sarvan13/Team9-Robot/ENPH257/DampedSquare.png

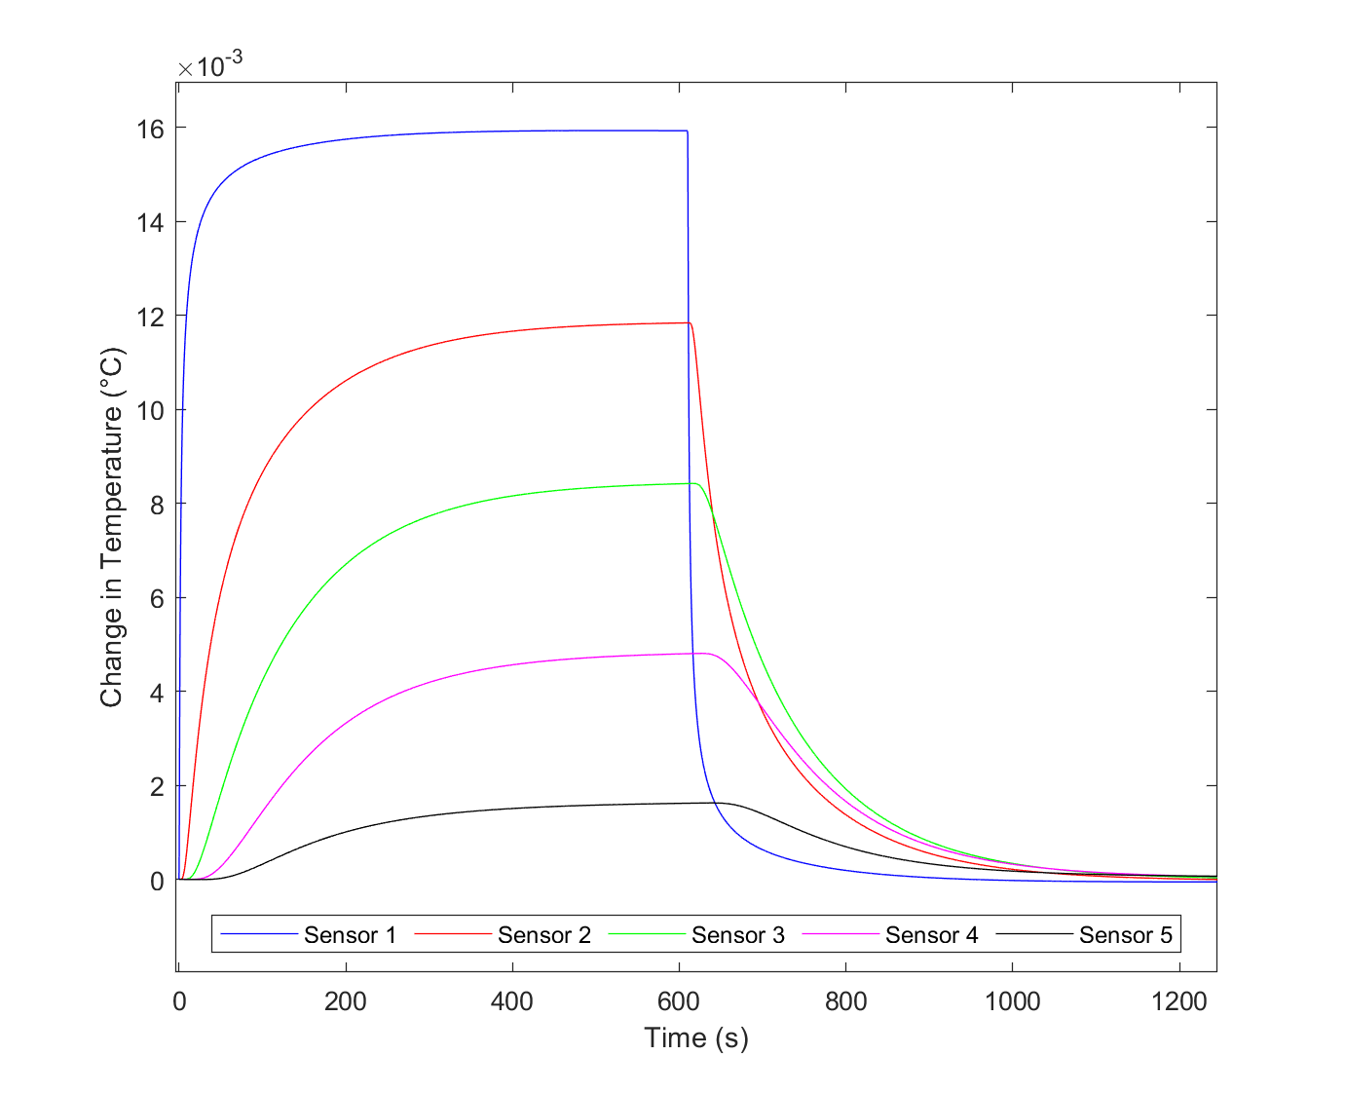
ENPH257/DampedSquare.png
