sarvan13/Team9-Robot/ENPH257/HorizontalFinal.png

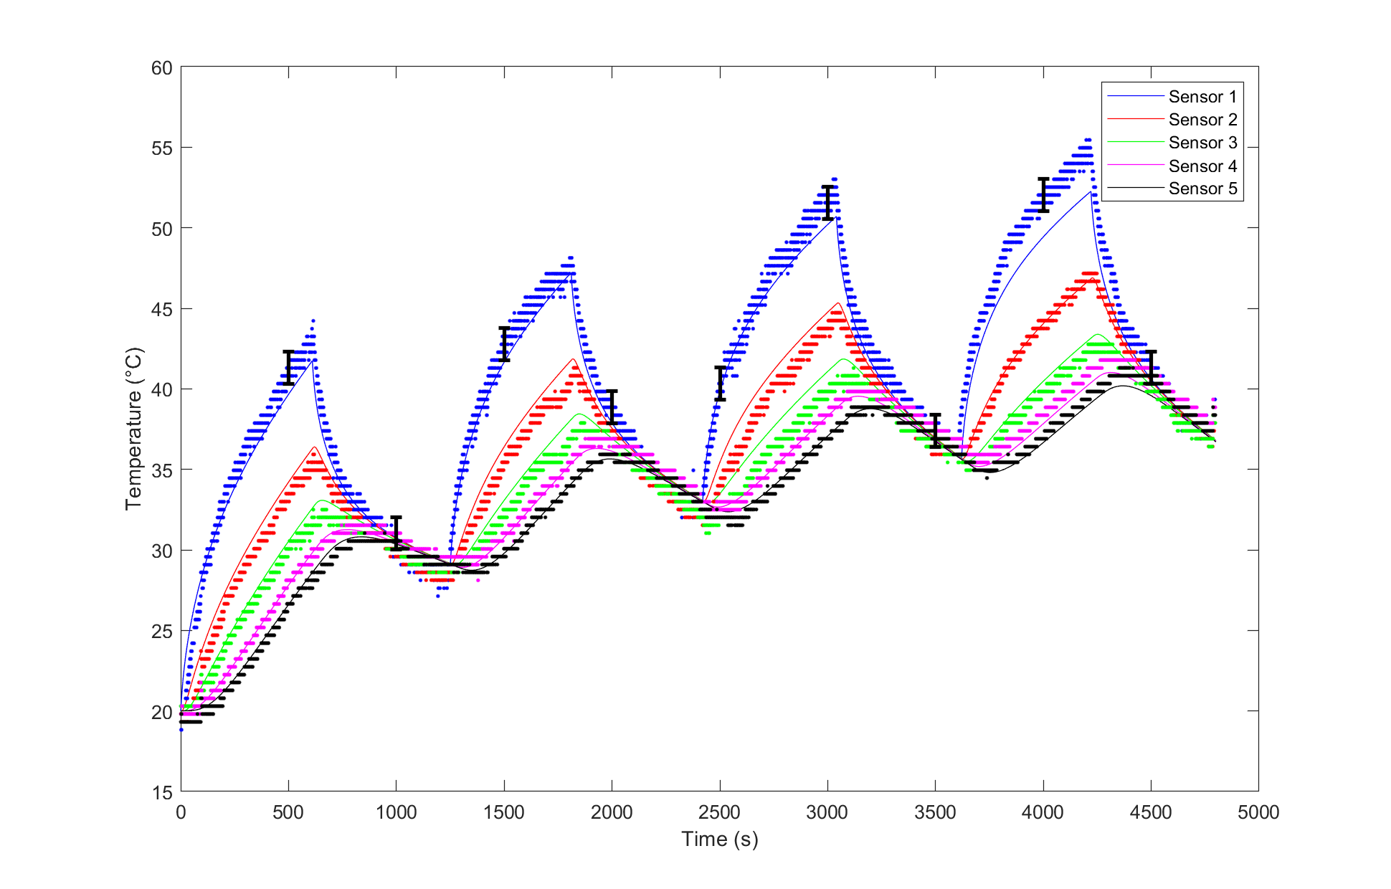
ENPH257/HorizontalFinal.png
