sarvan13/Team9-Robot/Solidworks/cutouts/chassis_cutout.SLDPRT

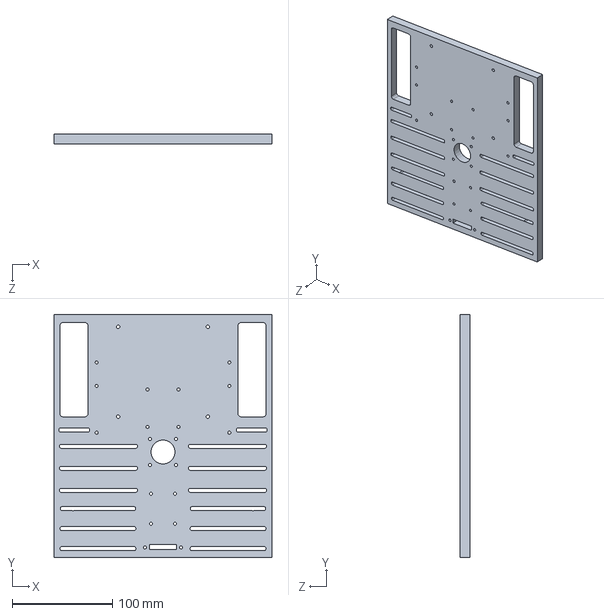
[picture p22: CAD file, 2019-07-09]
Solidworks/cutouts/chassis_cutout.SLDPRT
217.4 x 242.8 x 10.0 mm
