sarvan13/Team9-Robot/Solidworks/gears/36 teeth gear.SLDPRT

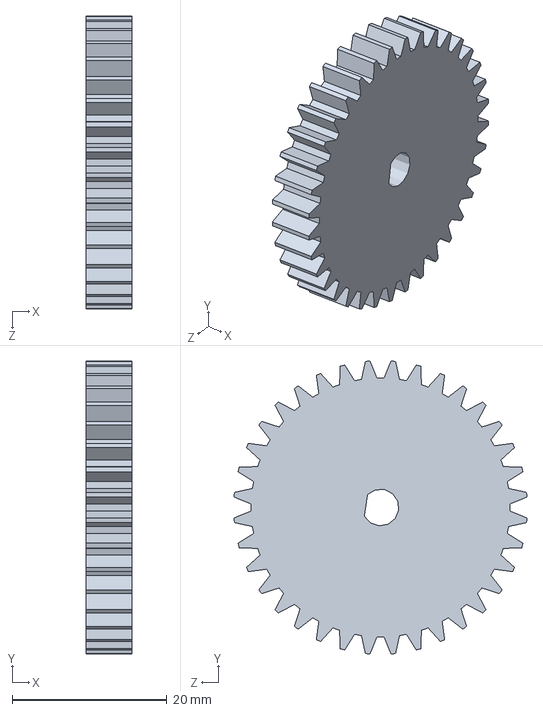
[picture p23: CAD file, 2019-07-24]
Solidworks/gears/36 teeth gear.SLDPRT
6.00 x 37.9 x 37.9 mm
