sarvan13/Team9-Robot/Solidworks/rightborder2.DXF

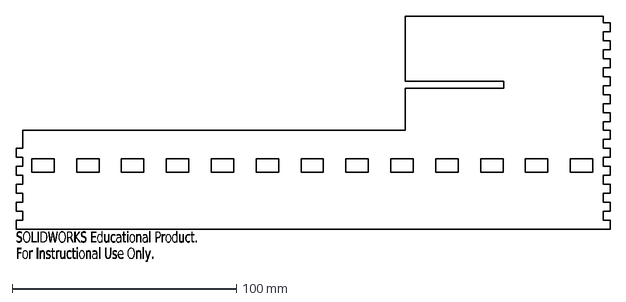
[picture p24: CAD file, 2019-08-04]
Solidworks/rightborder2.DXF
SOLIDWORKS Educational Product.
For Instructional Use Only.
