sarvan13/Team9-Robot/Solidworks/cutouts/motor_bracket.DXF

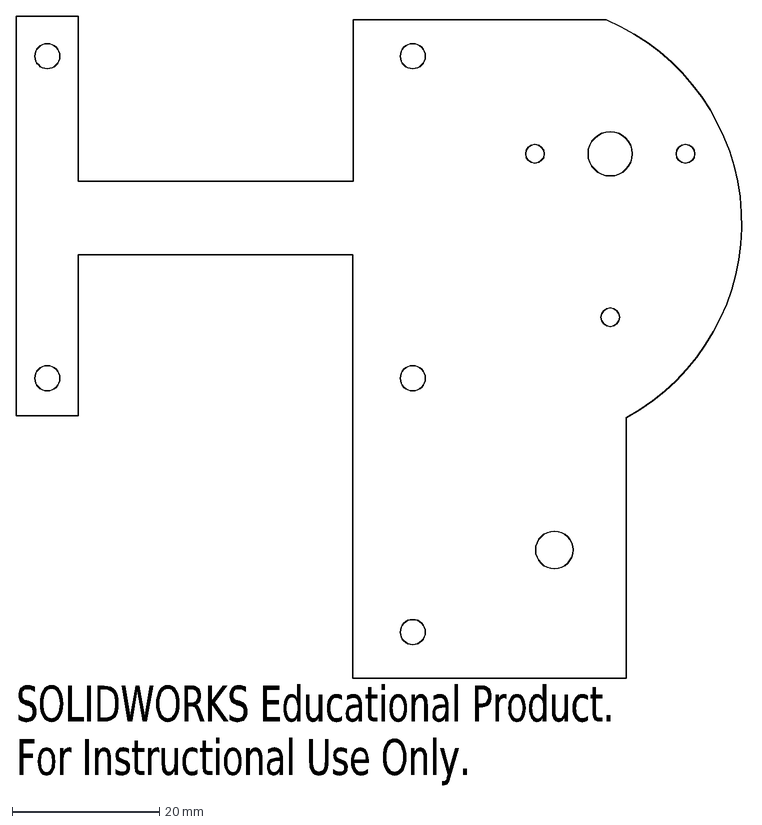
[picture p25: CAD file, 2019-07-08]
Solidworks/cutouts/motor_bracket.DXF
SOLIDWORKS Educational Product.
For Instructional Use Only.
