sarvan13/Team9-Robot/Solidworks/gears/16teethmoreoffset.DXF

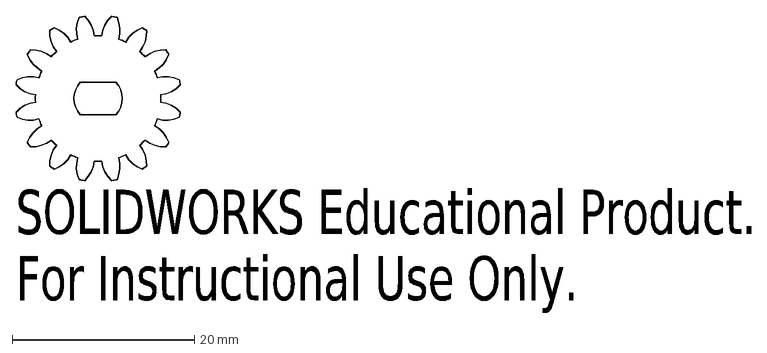
[picture p26: CAD file, 2019-07-24]
Solidworks/gears/16teethmoreoffset.DXF
SOLIDWORKS Educational Product.
For Instructional Use Only.
