sarvan13/Team9-Robot/Solidworks/rightbordernew.DXF

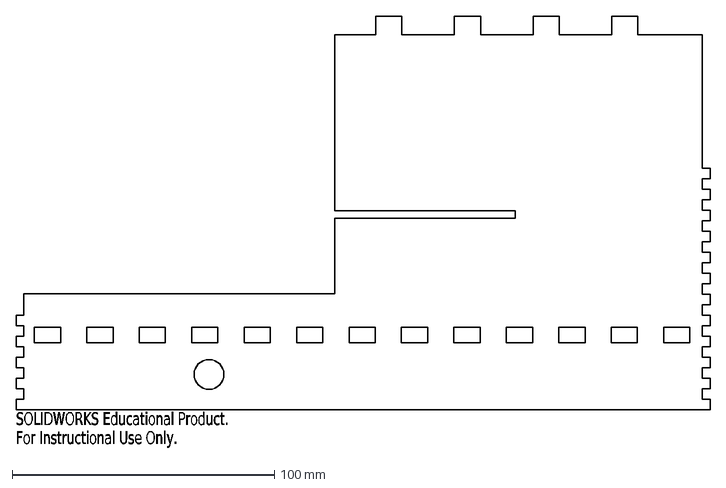
[picture p27: CAD file, 2019-08-04]
Solidworks/rightbordernew.DXF
SOLIDWORKS Educational Product.
For Instructional Use Only.
