sarvan13/Team9-Robot/Solidworks/gears/36GearThin.sldprt

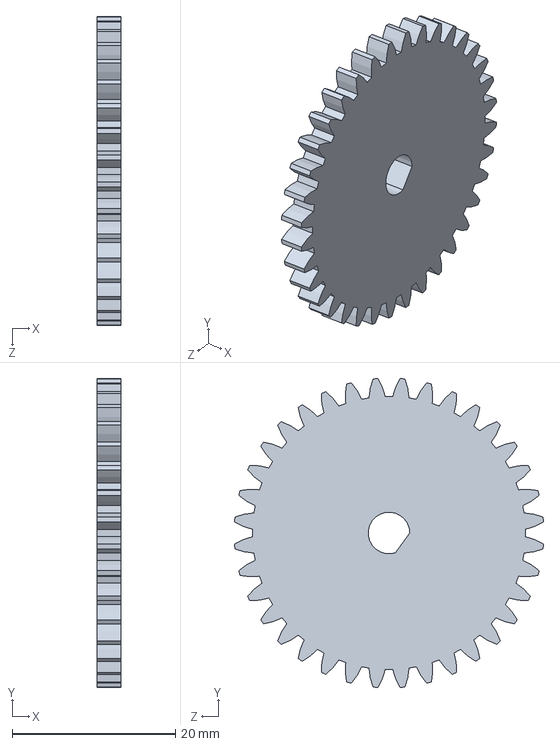
[picture p28: CAD file, 2019-07-15]
Solidworks/gears/36GearThin.sldprt
3.00 x 37.9 x 37.9 mm
