sarvan13/Team9-Robot/Solidworks/leftbordernewnew.DXF

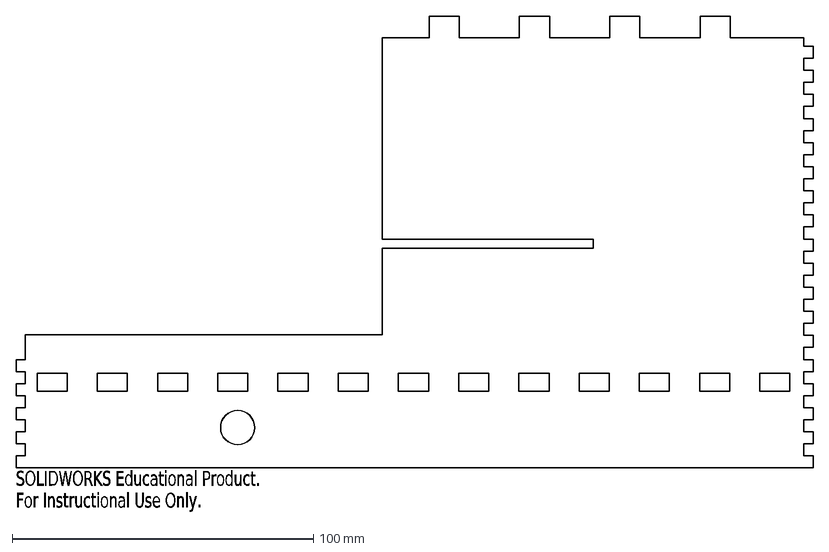
[picture p29: CAD file, 2019-08-04]
Solidworks/leftbordernewnew.DXF
SOLIDWORKS Educational Product.
For Instructional Use Only.
