sarvan13/Team9-Robot/Solidworks/chassis.sldprt

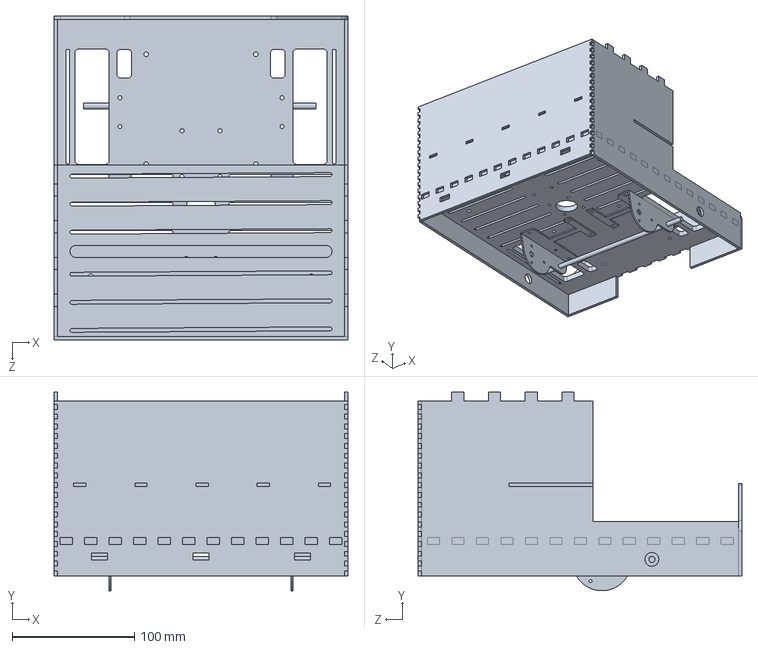
[picture p30: CAD file, 2019-08-04]
Solidworks/chassis.sldprt
240.0 x 162.1 x 264.6 mm
