sarvan13/Team9-Robot/Solidworks/cutouts/spacer_drivetrain_big_cutout.DXF

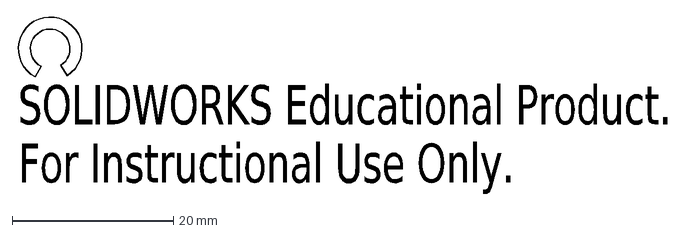
[picture p31: CAD file, 2019-07-08]
Solidworks/cutouts/spacer_drivetrain_big_cutout.DXF
SOLIDWORKS Educational Product.
For Instructional Use Only.
