sarvan13/Team9-Robot/Solidworks/gears/16TeethGearMod1.SLDPRT

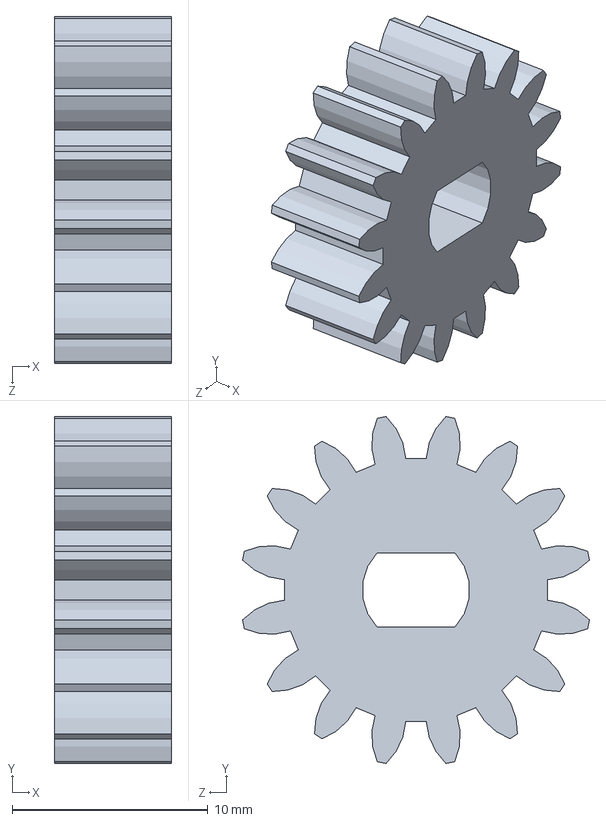
[picture p32: CAD file, 2019-07-15]
Solidworks/gears/16TeethGearMod1.SLDPRT
6.00 x 17.7 x 17.7 mm
