sarvan13/Team9-Robot/Solidworks/cutouts/spacer_platter_small_cutout.DXF

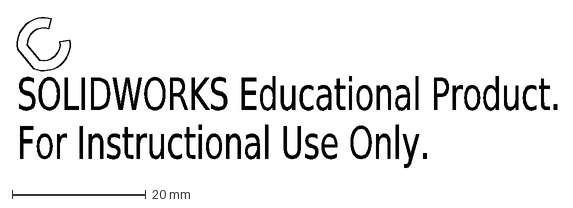
[picture p33: CAD file, 2019-07-08]
Solidworks/cutouts/spacer_platter_small_cutout.DXF
SOLIDWORKS Educational Product.
For Instructional Use Only.
