sarvan13/Team9-Robot/Solidworks/gears/126 teeth gear.SLDPRT

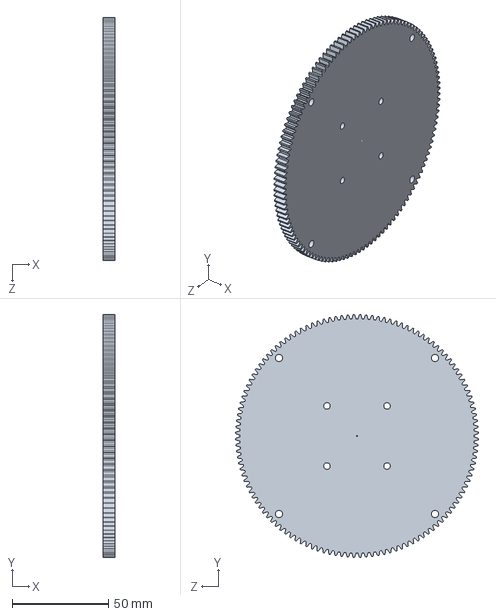
[picture p34: CAD file, 2019-07-15]
Solidworks/gears/126 teeth gear.SLDPRT
6.00 x 126.0 x 126.0 mm
