sarvan13/Team9-Robot/Solidworks/leftbordernew.DXF

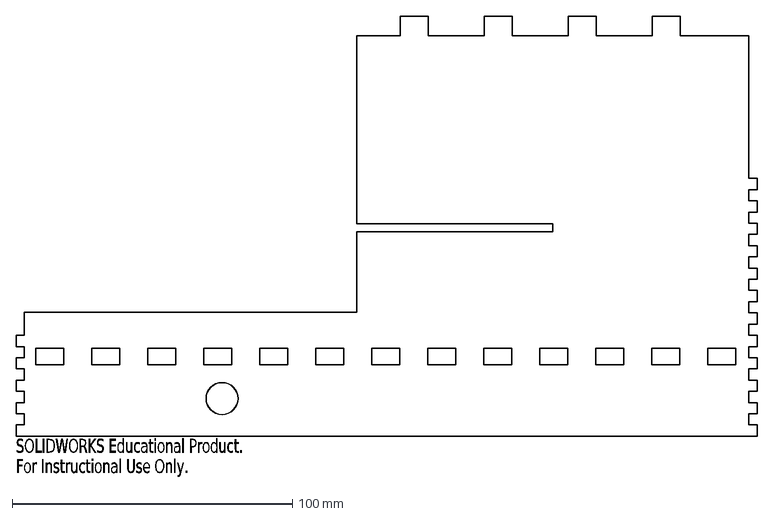
[picture p35: CAD file, 2019-08-04]
Solidworks/leftbordernew.DXF
SOLIDWORKS Educational Product.
For Instructional Use Only.
