sarvan13/Team9-Robot/Solidworks/cutouts/iso_spur_platter_small_cutout.SLDPRT

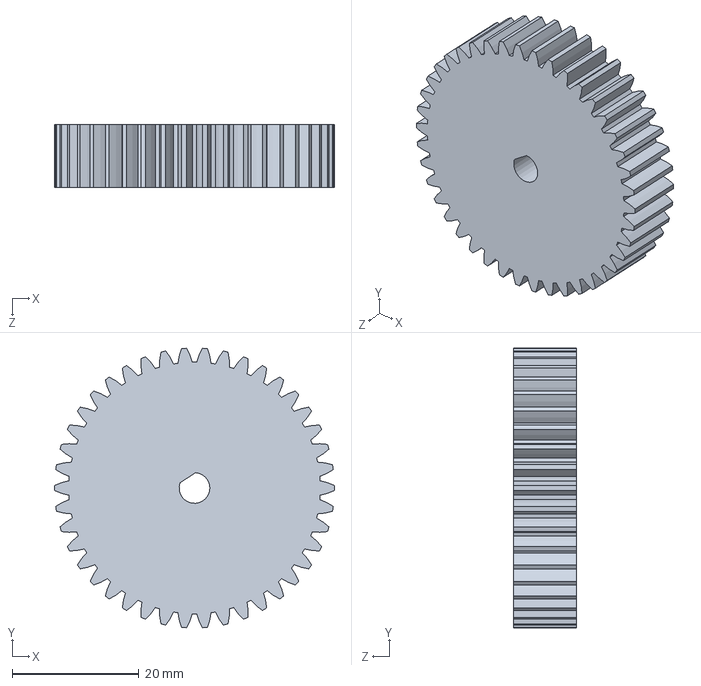
[picture p36: CAD file, 2019-07-08]
Solidworks/cutouts/iso_spur_platter_small_cutout.SLDPRT
44.2 x 44.2 x 10.0 mm
