sarvan13/Team9-Robot/Solidworks/rightbackborder.DXF

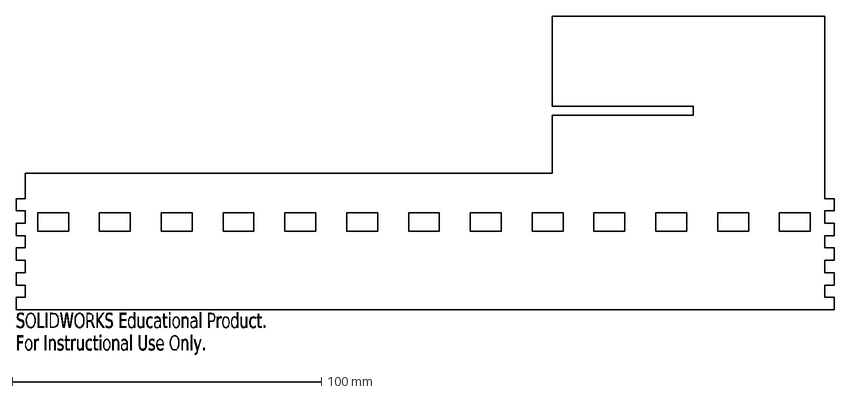
[picture p37: CAD file, 2019-08-04]
Solidworks/rightbackborder.DXF
SOLIDWORKS Educational Product.
For Instructional Use Only.
