sarvan13/Team9-Robot/Solidworks/cutouts/iso_spur_drivetrain_small_cutout.SLDPRT

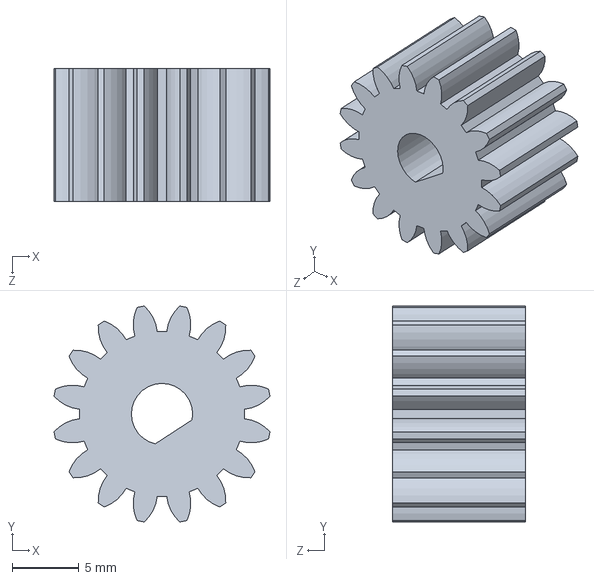
[picture p38: CAD file, 2019-07-08]
Solidworks/cutouts/iso_spur_drivetrain_small_cutout.SLDPRT
16.2 x 16.2 x 10.0 mm
