sarvan13/Team9-Robot/Solidworks/gears/16TeethGearMod1v1Offset.DXF

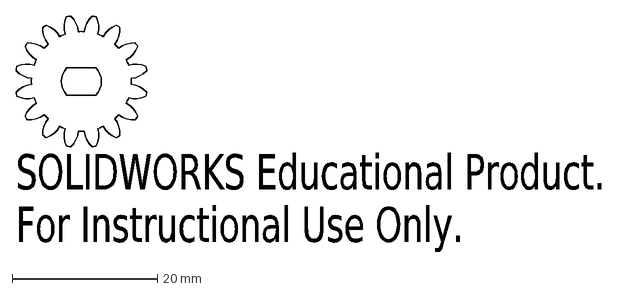
[picture p39: CAD file, 2019-07-14]
Solidworks/gears/16TeethGearMod1v1Offset.DXF
SOLIDWORKS Educational Product.
For Instructional Use Only.
