sarvan13/Team9-Robot/Solidworks/cutouts/iso_spur_drivetrain_big_cutout.SLDPRT

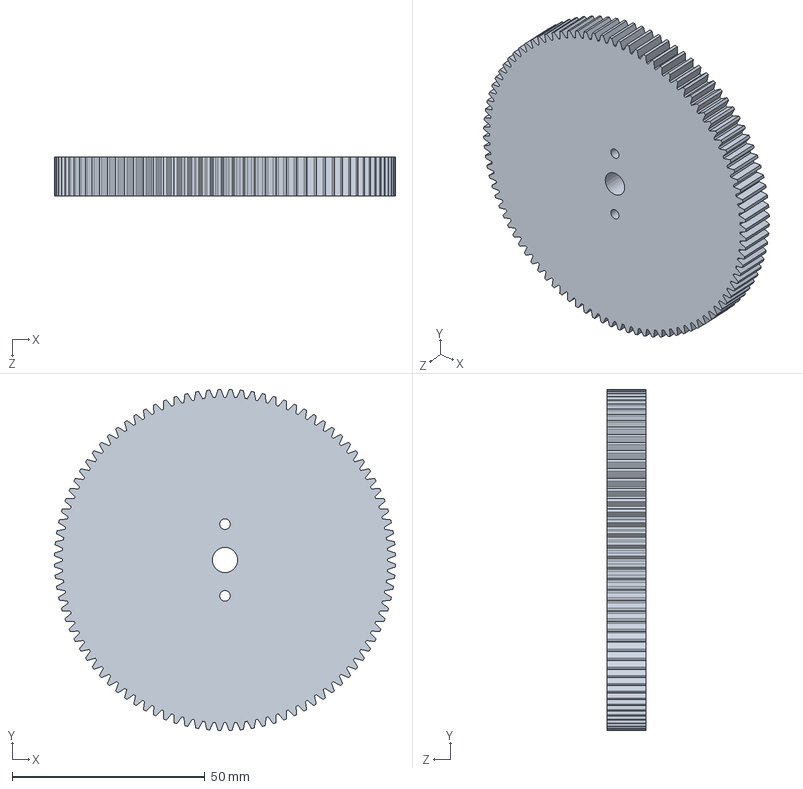
[picture p40: CAD file, 2019-07-08]
Solidworks/cutouts/iso_spur_drivetrain_big_cutout.SLDPRT
88.4 x 88.4 x 10.0 mm
