sarvan13/Team9-Robot/Solidworks/gears/16TeethGearMod1v1.DXF

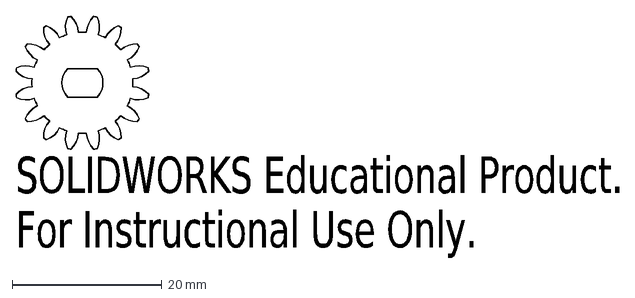
[picture p41: CAD file, 2019-07-14]
Solidworks/gears/16TeethGearMod1v1.DXF
SOLIDWORKS Educational Product.
For Instructional Use Only.
