sarvan13/Team9-Robot/Solidworks/shelfnew.DXF

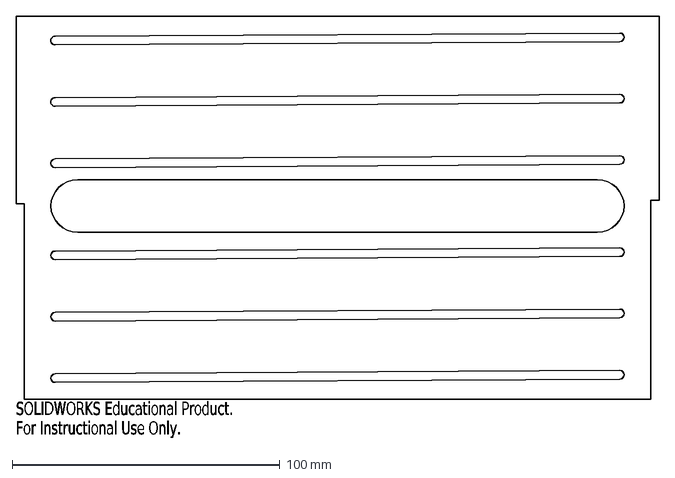
[picture p42: CAD file, 2019-08-04]
Solidworks/shelfnew.DXF
SOLIDWORKS Educational Product.
For Instructional Use Only.
