sarvan13/Team9-Robot/Solidworks/cutouts/chassis_cutout_wj.DXF

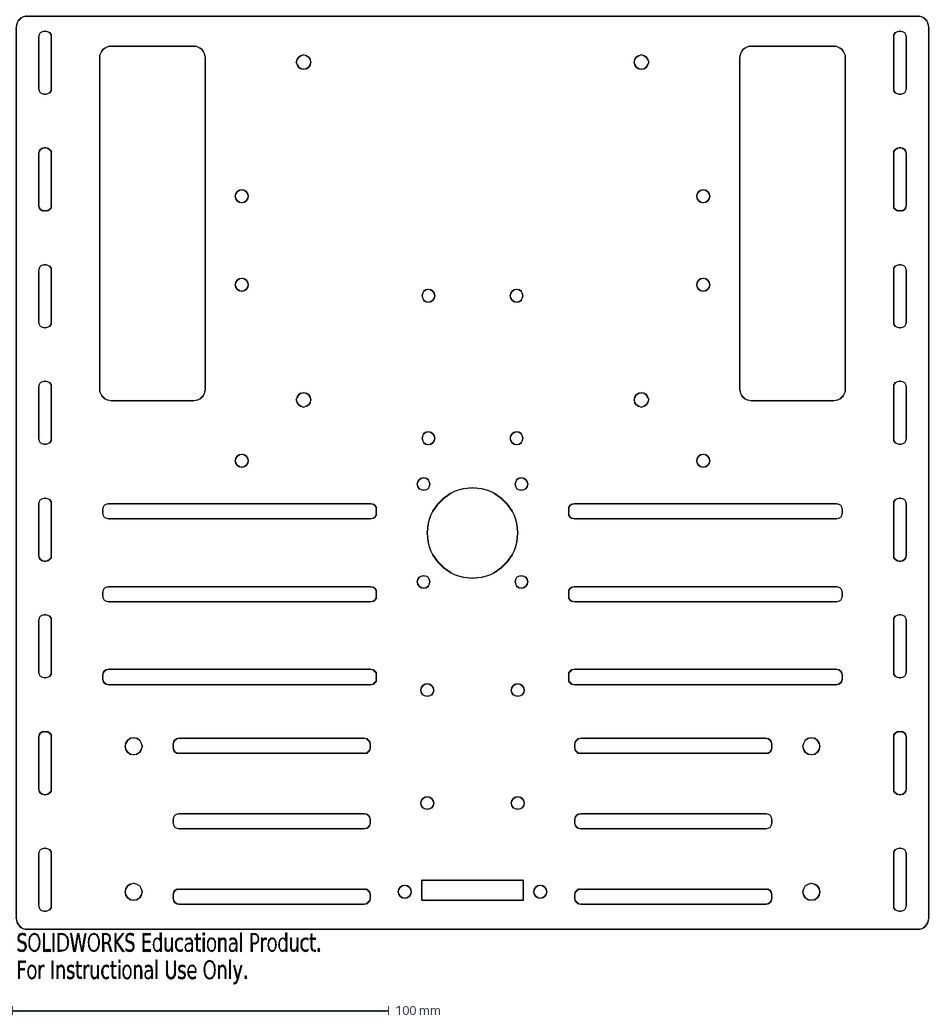
[picture p43: CAD file, 2019-07-08]
Solidworks/cutouts/chassis_cutout_wj.DXF
SOLIDWORKS Educational Product.
For Instructional Use Only.
