sarvan13/Team9-Robot/Solidworks/frontbordernewnew.DXF

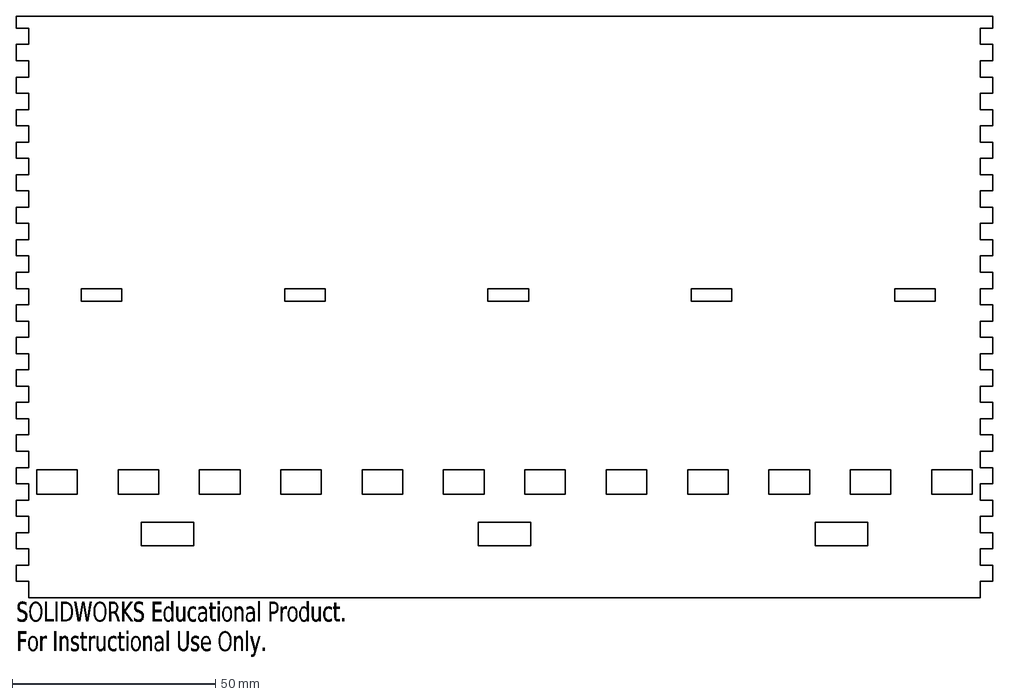
[picture p44: CAD file, 2019-08-04]
Solidworks/frontbordernewnew.DXF
SOLIDWORKS Educational Product.
For Instructional Use Only.
