sarvan13/Team9-Robot/Solidworks/cutouts/spacer_drivetrain_small_cutout.DXF

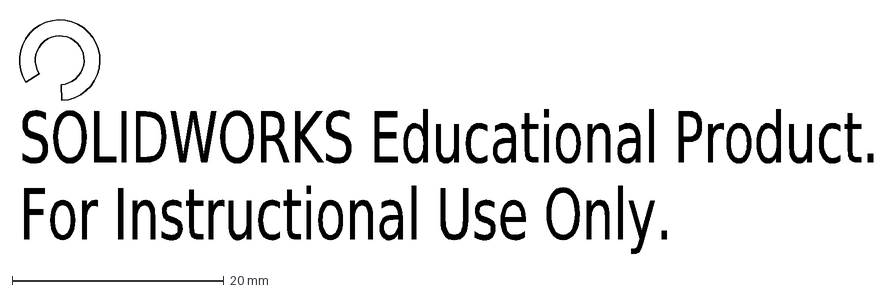
[picture p45: CAD file, 2019-07-08]
Solidworks/cutouts/spacer_drivetrain_small_cutout.DXF
SOLIDWORKS Educational Product.
For Instructional Use Only.
