sarvan13/Team9-Robot/Solidworks/leftborder.DXF

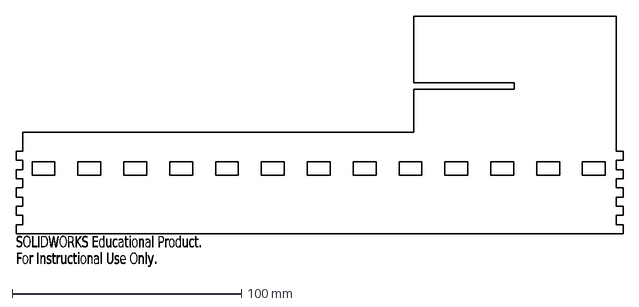
[picture p46: CAD file, 2019-08-04]
Solidworks/leftborder.DXF
SOLIDWORKS Educational Product.
For Instructional Use Only.
