sarvan13/Team9-Robot/Solidworks/backbordernew.DXF

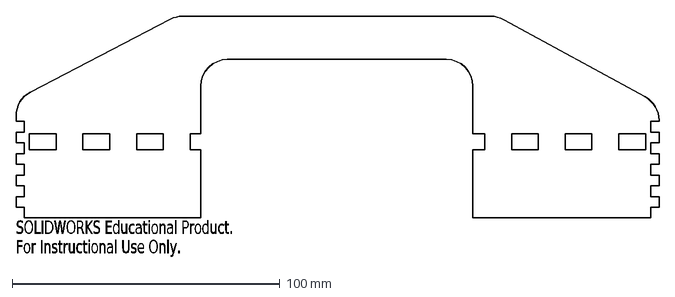
[picture p47: CAD file, 2019-08-04]
Solidworks/backbordernew.DXF
SOLIDWORKS Educational Product.
For Instructional Use Only.
