sarvan13/Team9-Robot/Solidworks/leftborder2.DXF

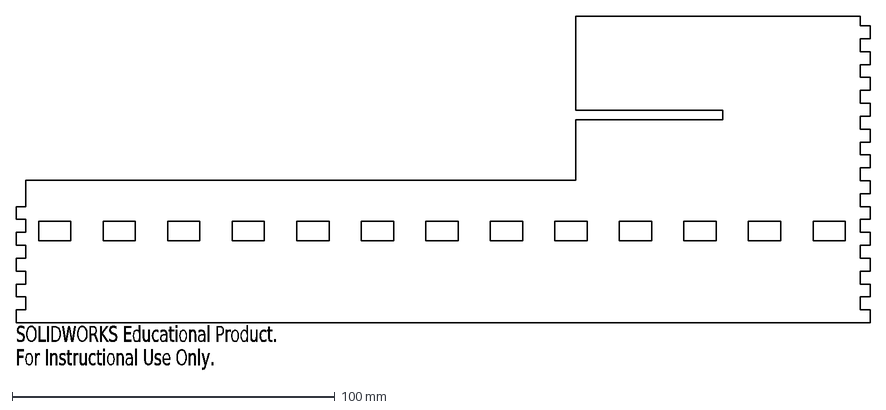
[picture p48: CAD file, 2019-08-04]
Solidworks/leftborder2.DXF
SOLIDWORKS Educational Product.
For Instructional Use Only.
