sarvan13/Team9-Robot/Solidworks/rightbordernewnew.DXF

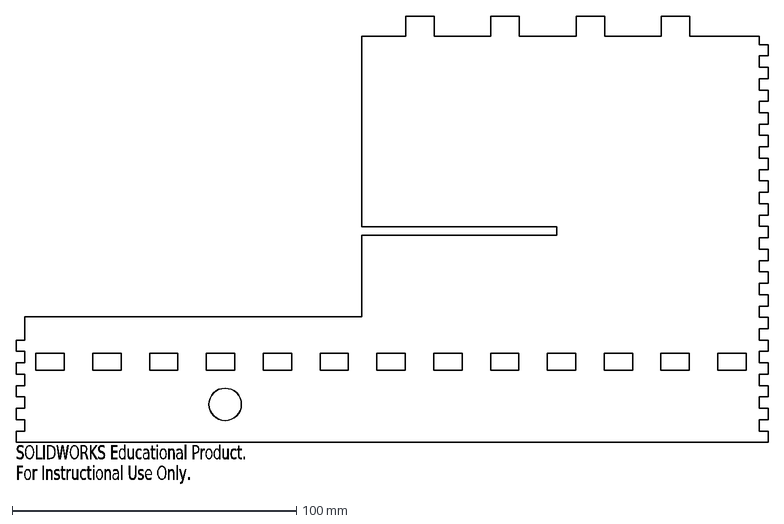
[picture p49: CAD file, 2019-08-04]
Solidworks/rightbordernewnew.DXF
SOLIDWORKS Educational Product.
For Instructional Use Only.
