sarvan13/Team9-Robot/Solidworks/storeshelf.DXF

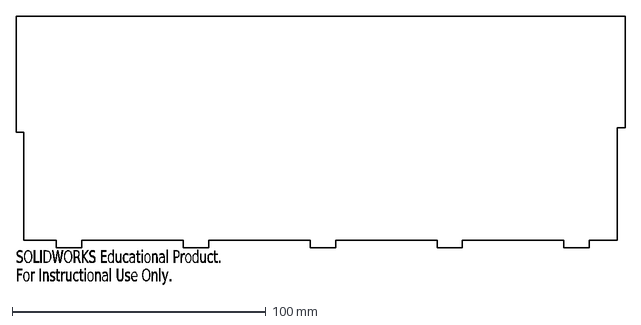
[picture p50: CAD file, 2019-08-04]
Solidworks/storeshelf.DXF
SOLIDWORKS Educational Product.
For Instructional Use Only.
