sarvan13/Team9-Robot/Solidworks/backborder.DXF

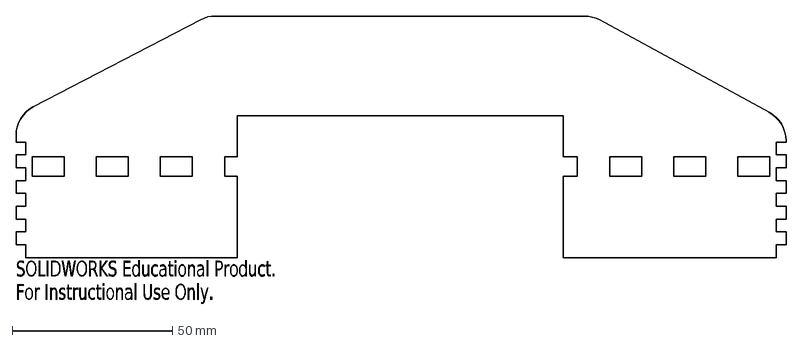
[picture p51: CAD file, 2019-08-04]
Solidworks/backborder.DXF
SOLIDWORKS Educational Product.
For Instructional Use Only.
