sarvan13/Team9-Robot/Solidworks/frontborder2.DXF

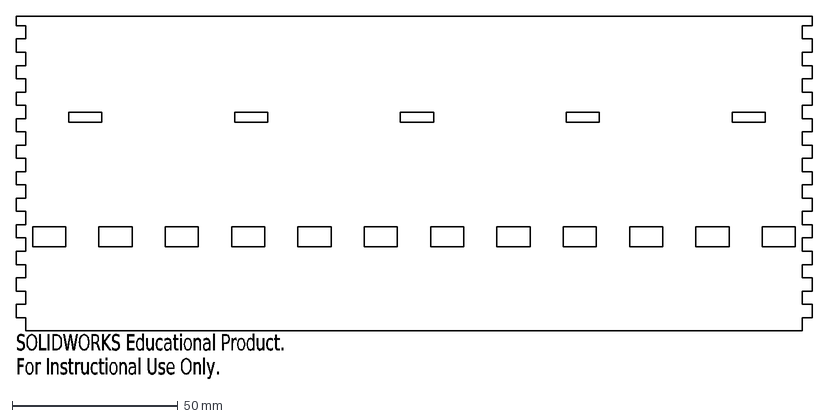
[picture p52: CAD file, 2019-08-04]
Solidworks/frontborder2.DXF
SOLIDWORKS Educational Product.
For Instructional Use Only.
