sarvan13/Team9-Robot/Solidworks/shelfnewnew.DXF

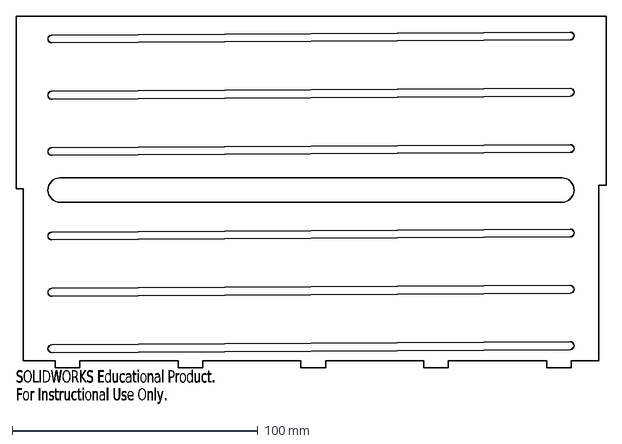
[picture p53: CAD file, 2019-08-04]
Solidworks/shelfnewnew.DXF
SOLIDWORKS Educational Product.
For Instructional Use Only.
