sarvan13/Team9-Robot/Solidworks/NutPlate.SLDPRT

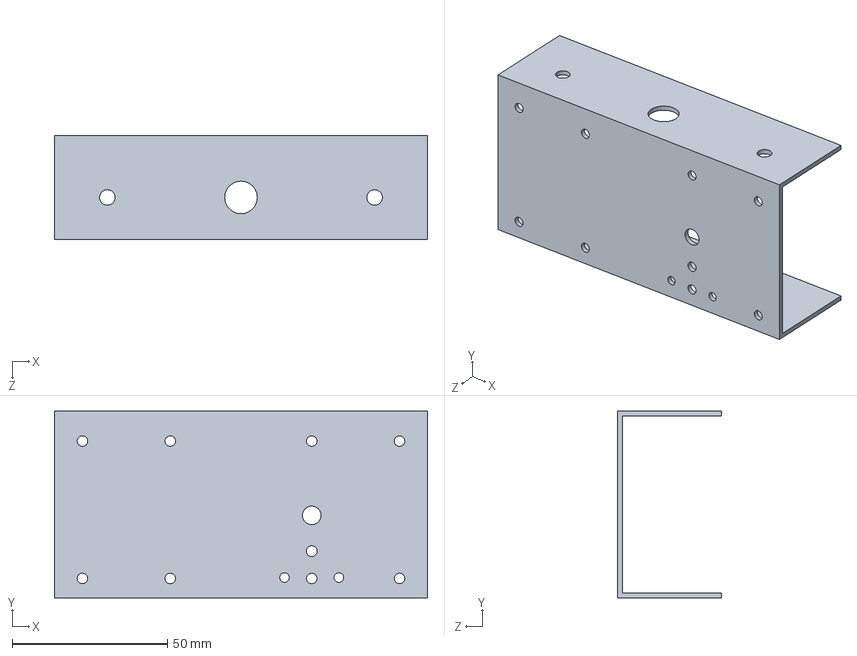
[picture p54: CAD file, 2019-07-25]
Solidworks/NutPlate.SLDPRT
120.0 x 60.0 x 33.6 mm
