sarvan13/Team9-Robot/Solidworks/TopStabilizer.SLDPRT

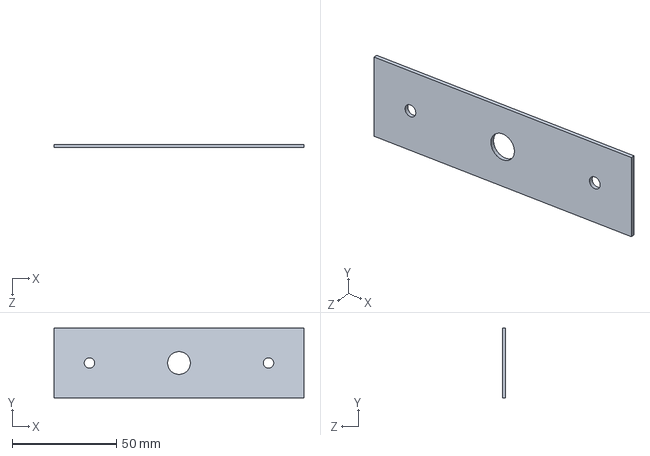
[picture p55: CAD file, 2019-07-25]
Solidworks/TopStabilizer.SLDPRT
120.0 x 33.6 x 1.60 mm
