sarvan13/Team9-Robot/Solidworks/RackCircuitMountSide.SLDPRT

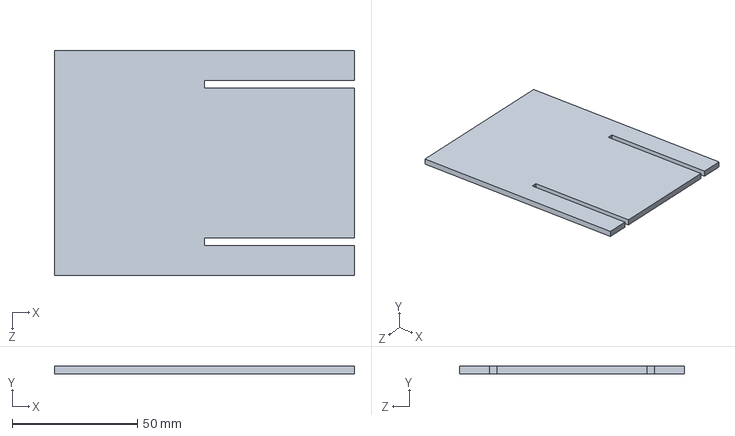
[picture p56: CAD file, 2019-07-24]
Solidworks/RackCircuitMountSide.SLDPRT
120.0 x 3.00 x 90.0 mm
