sarvan13/Team9-Robot/Solidworks/RackCircuitMountTop.SLDPRT

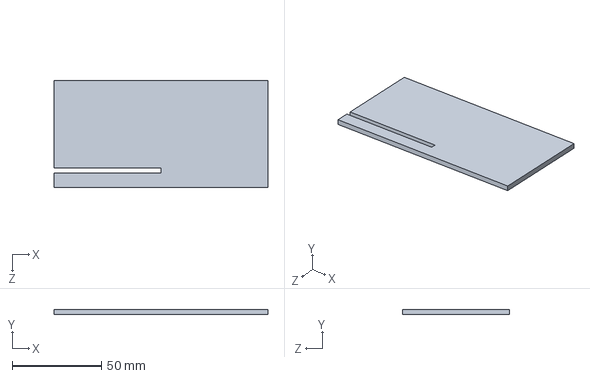
[picture p57: CAD file, 2019-07-24]
Solidworks/RackCircuitMountTop.SLDPRT
120.0 x 3.00 x 60.0 mm
