sarvan13/Team9-Robot/Solidworks/switch_panel.SLDPRT

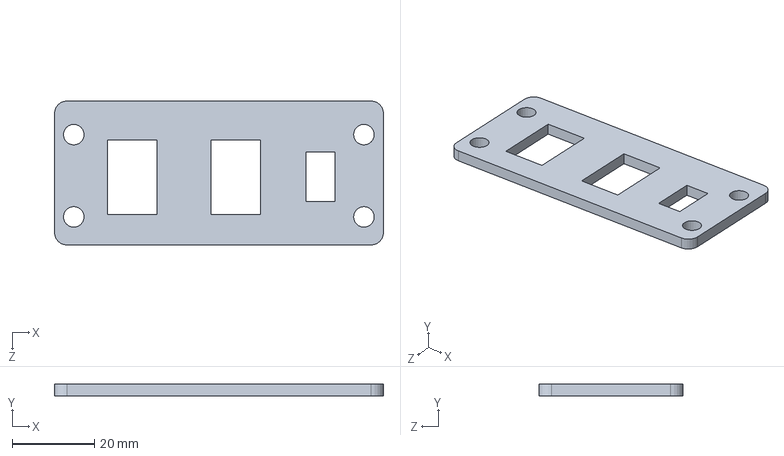
[picture p58: CAD file, 2019-07-15]
Solidworks/switch_panel.SLDPRT
80.0 x 3.00 x 35.0 mm
