sarvan13/Team9-Robot/Solidworks/robot shop caster RB dag 22.SLDPRT

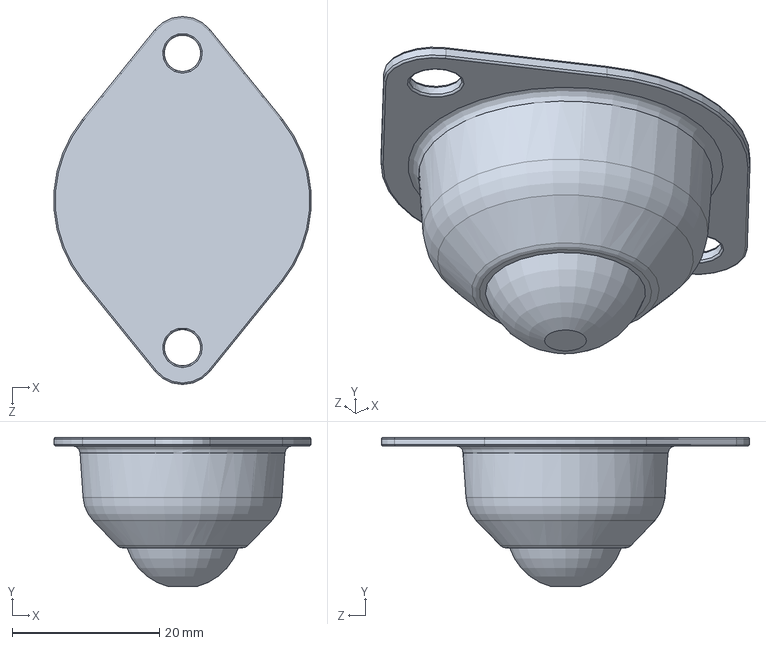
[picture p59: CAD file, 2019-07-15]
Solidworks/robot shop caster RB dag 22.SLDPRT
34.9 x 20.2 x 50.0 mm
