sarvan13/Team9-Robot/Solidworks/RackChanel.SLDPRT

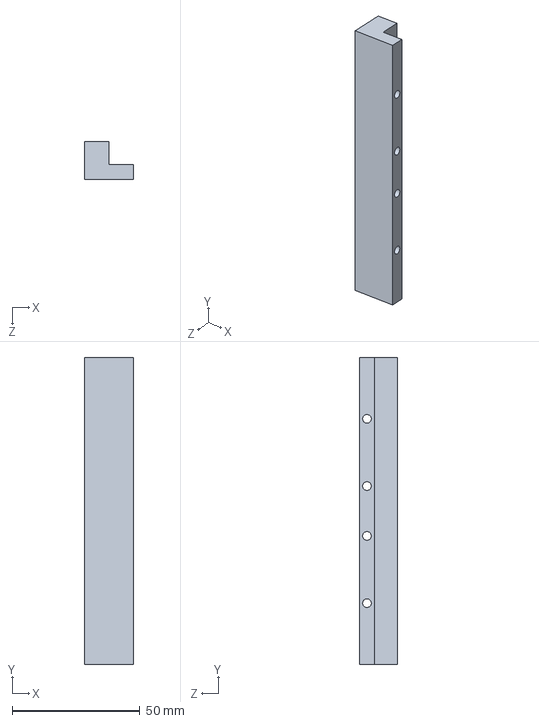
[picture p60: CAD file, 2019-07-15]
Solidworks/RackChanel.SLDPRT
19.0 x 120.0 x 15.0 mm
