sarvan13/Team9-Robot/Solidworks/post.SLDPRT

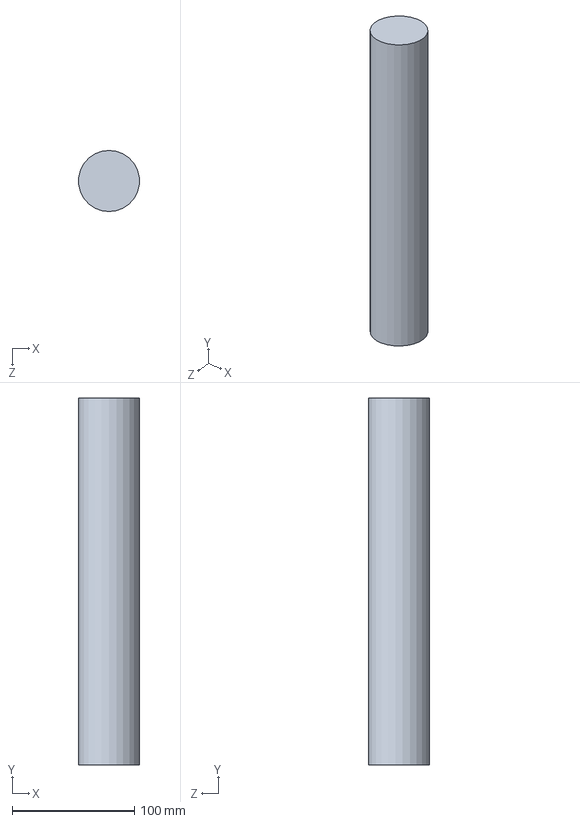
[picture p61: CAD file, 2019-07-15]
Solidworks/post.SLDPRT
49.6 x 300.0 x 50.0 mm
