sarvan13/Team9-Robot/Solidworks/Motor-BarbCole-Ungeared.sldprt

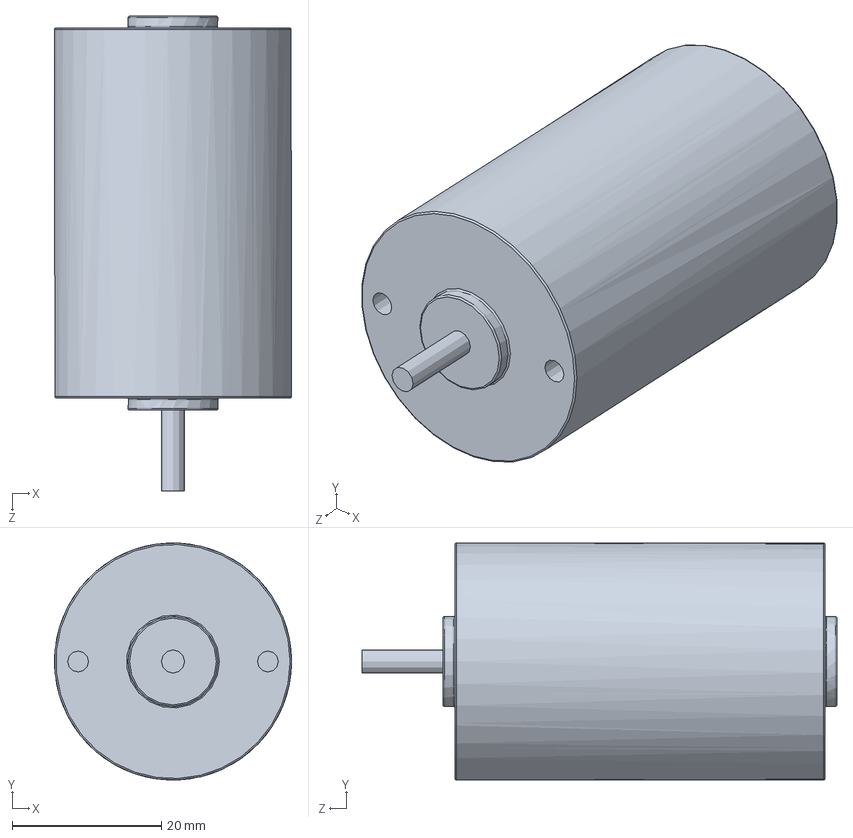
[picture p62: CAD file, 2019-07-15]
Solidworks/Motor-BarbCole-Ungeared.sldprt
31.8 x 31.7 x 63.6 mm
