sarvan13/Team9-Robot/Solidworks/Step Motor 28BYJ-48.SLDPRT

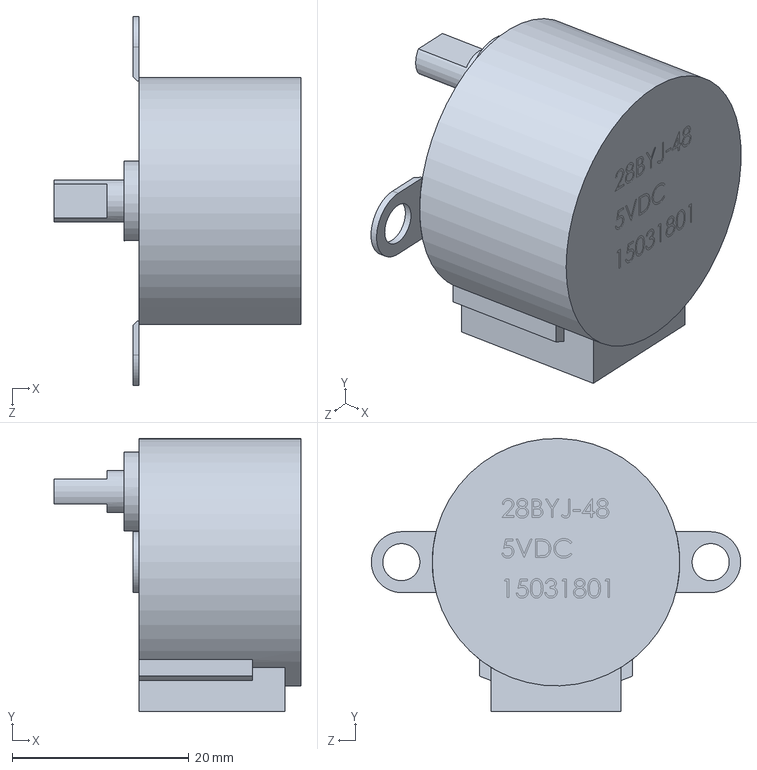
[picture p63: CAD file, 2019-07-15]
Solidworks/Step Motor 28BYJ-48.SLDPRT
27.9 x 30.9 x 41.8 mm
