sarvan13/Team9-Robot/Solidworks/Motor BarbCole Geared.SLDPRT

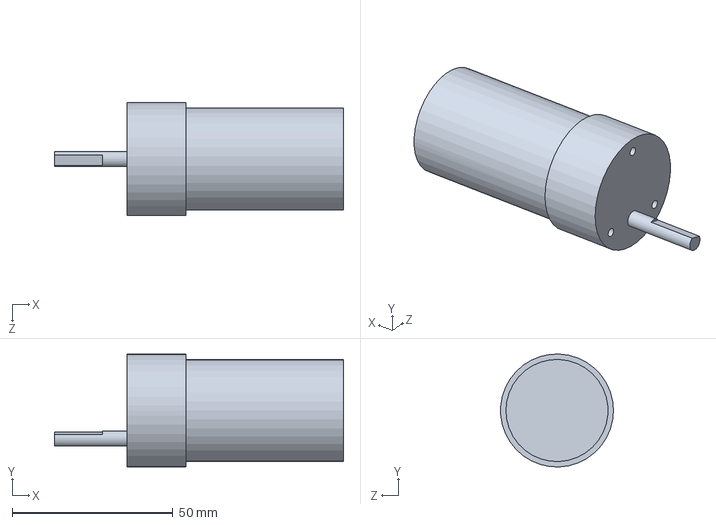
[picture p64: CAD file, 2019-07-15]
Solidworks/Motor BarbCole Geared.SLDPRT
89.9 x 35.1 x 35.1 mm
