sarvan13/Team9-Robot/Solidworks/stepper_motor.SLDPRT

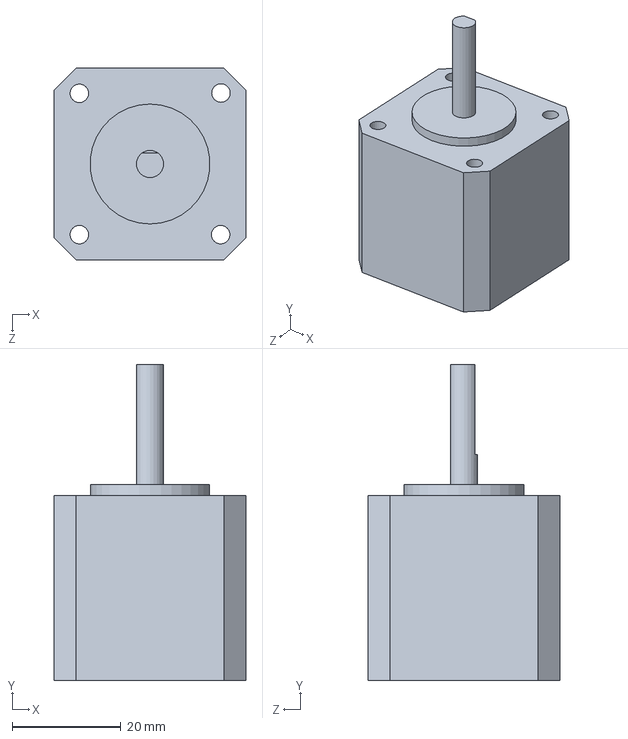
[picture p65: CAD file, 2019-07-15]
Solidworks/stepper_motor.SLDPRT
35.2 x 58.0 x 35.2 mm
