sarvan13/Team9-Robot/Solidworks/spacer_platter_small.SLDPRT

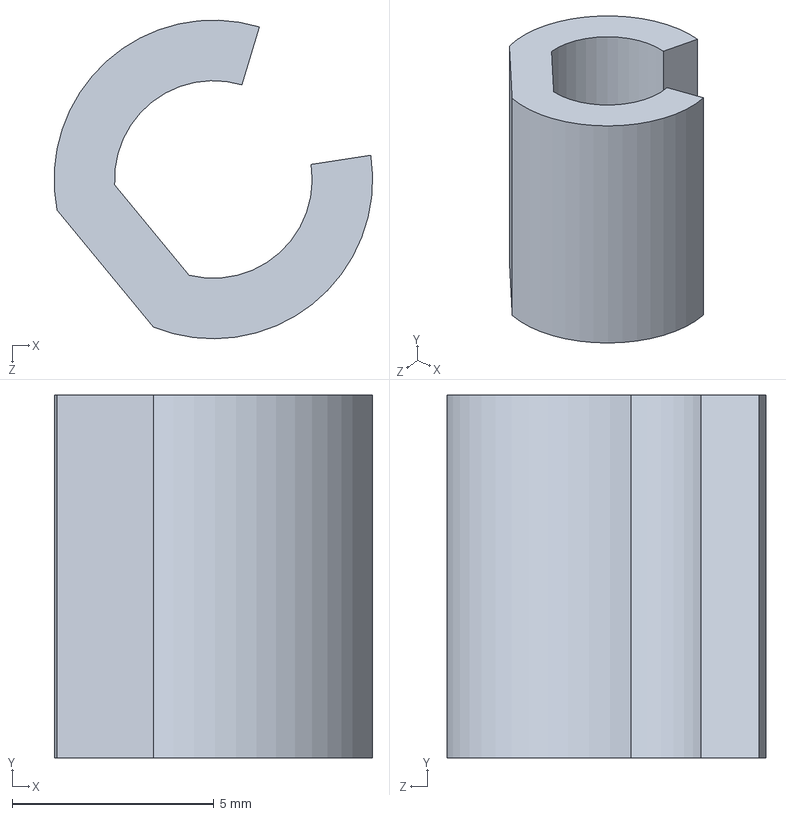
[picture p66: CAD file, 2019-07-15]
Solidworks/spacer_platter_small.SLDPRT
7.89 x 9.00 x 7.90 mm
