sarvan13/Team9-Robot/Solidworks/Rack.sldprt

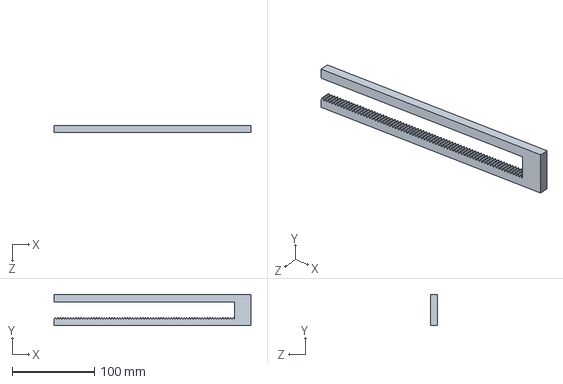
[picture p67: CAD file, 2019-07-15]
Solidworks/Rack.sldprt
240.0 x 38.0 x 9.00 mm
