sarvan13/Team9-Robot/Solidworks/iso_spur_platter_small.SLDPRT

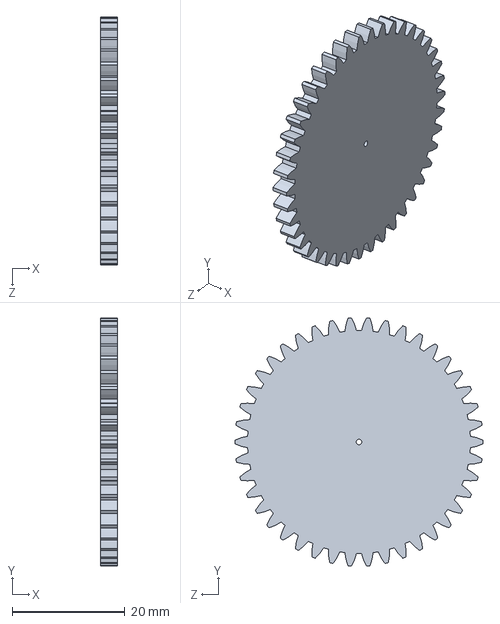
[picture p68: CAD file, 2019-07-15]
Solidworks/iso_spur_platter_small.SLDPRT
3.00 x 43.9 x 44.0 mm
