sarvan13/Team9-Robot/Solidworks/arm_block.sldprt

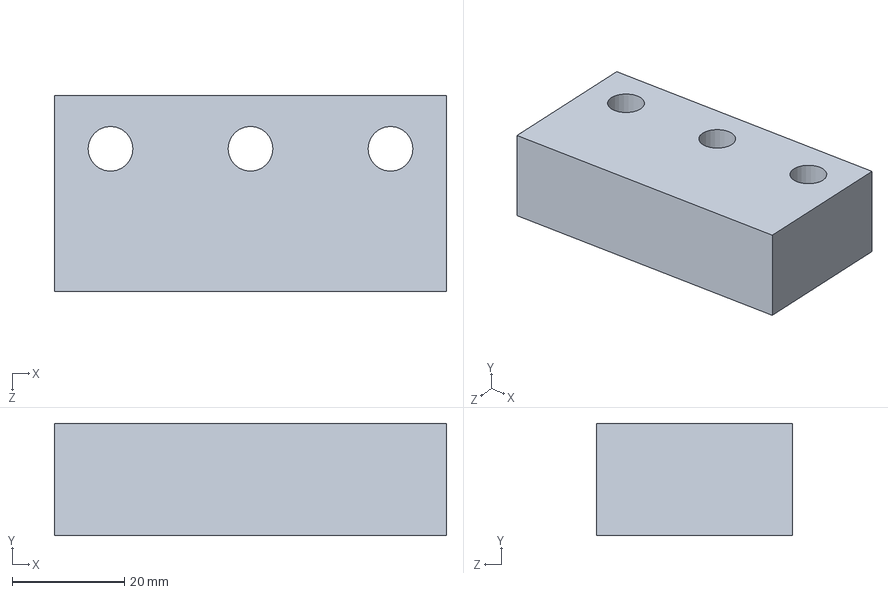
[picture p69: CAD file, 2019-07-15]
Solidworks/arm_block.sldprt
70.0 x 20.0 x 35.0 mm
