sarvan13/Team9-Robot/Solidworks/arm_base.sldprt

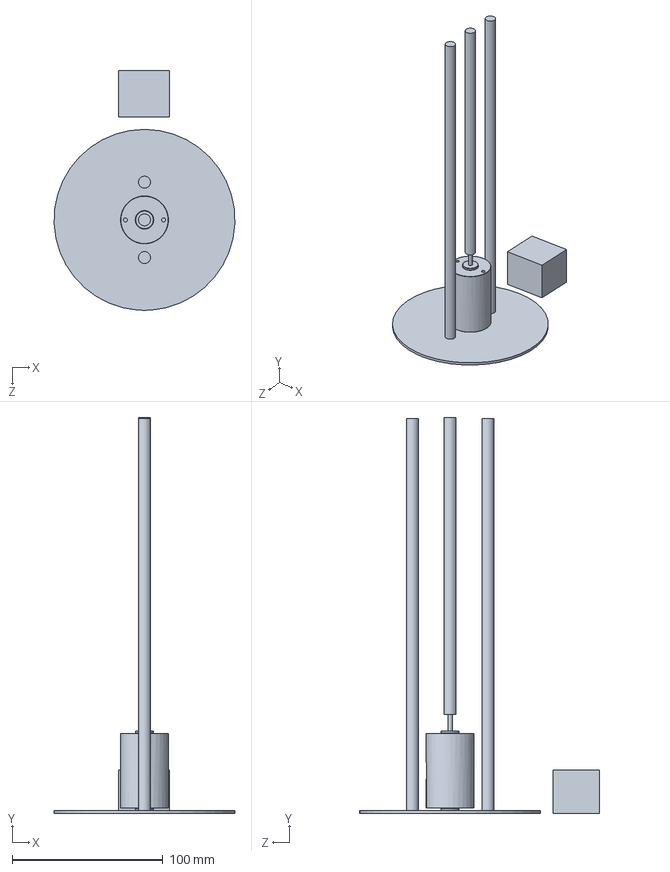
[picture p70: CAD file, 2019-07-15]
Solidworks/arm_base.sldprt
119.9 x 262.6 x 158.9 mm
