sarvan13/Team9-Robot/Solidworks/FrontBumper.SLDPRT

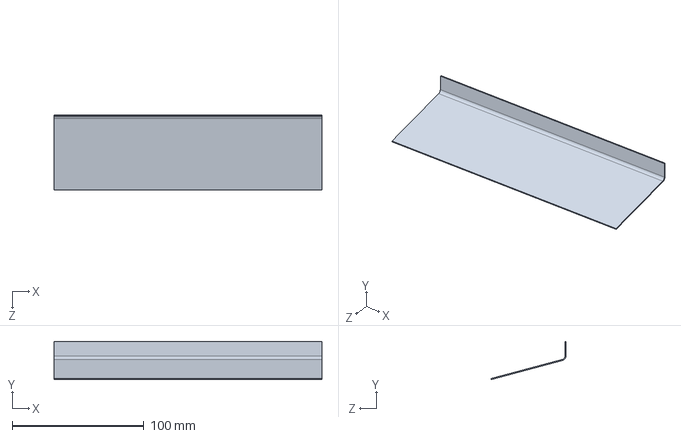
[picture p71: CAD file, 2019-07-15]
Solidworks/FrontBumper.SLDPRT
203.2 x 28.9 x 56.9 mm
