sarvan13/Team9-Robot/Solidworks/funnel_insert_v2.SLDPRT

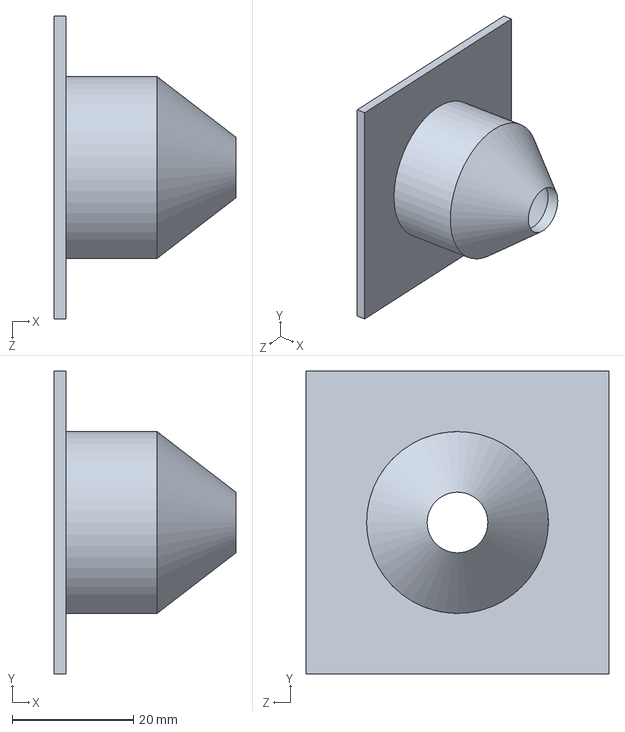
[picture p72: CAD file, 2019-07-15]
Solidworks/funnel_insert_v2.SLDPRT
30.0 x 50.0 x 50.0 mm
