sarvan13/Team9-Robot/Solidworks/wheel.sldprt

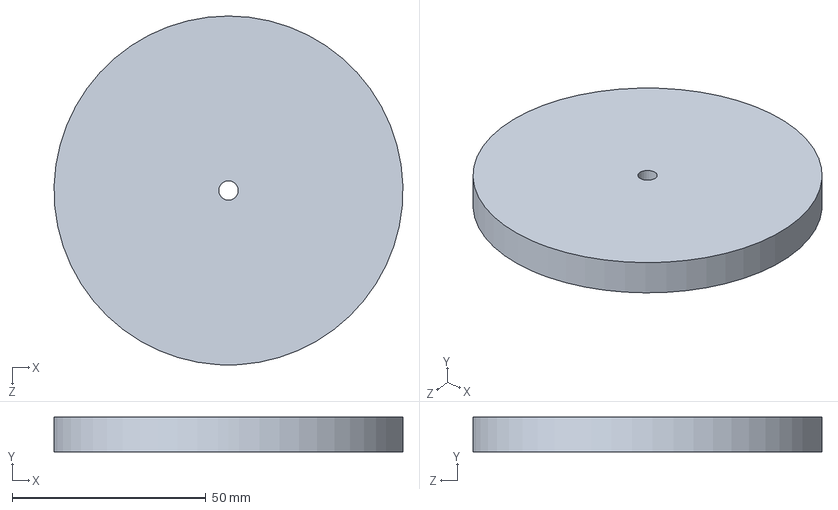
[picture p73: CAD file, 2019-07-15]
Solidworks/wheel.sldprt
90.0 x 9.00 x 90.0 mm
