sarvan13/Team9-Robot/Solidworks/caster.sldprt

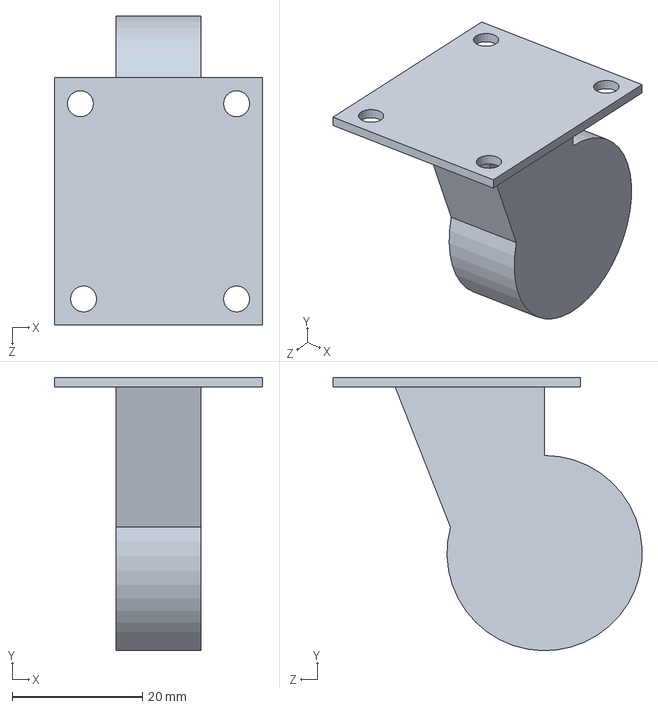
[picture p74: CAD file, 2019-07-15]
Solidworks/caster.sldprt
32.0 x 42.0 x 47.5 mm
