sarvan13/Team9-Robot/Solidworks/Rod2CBraketBraket.SLDPRT

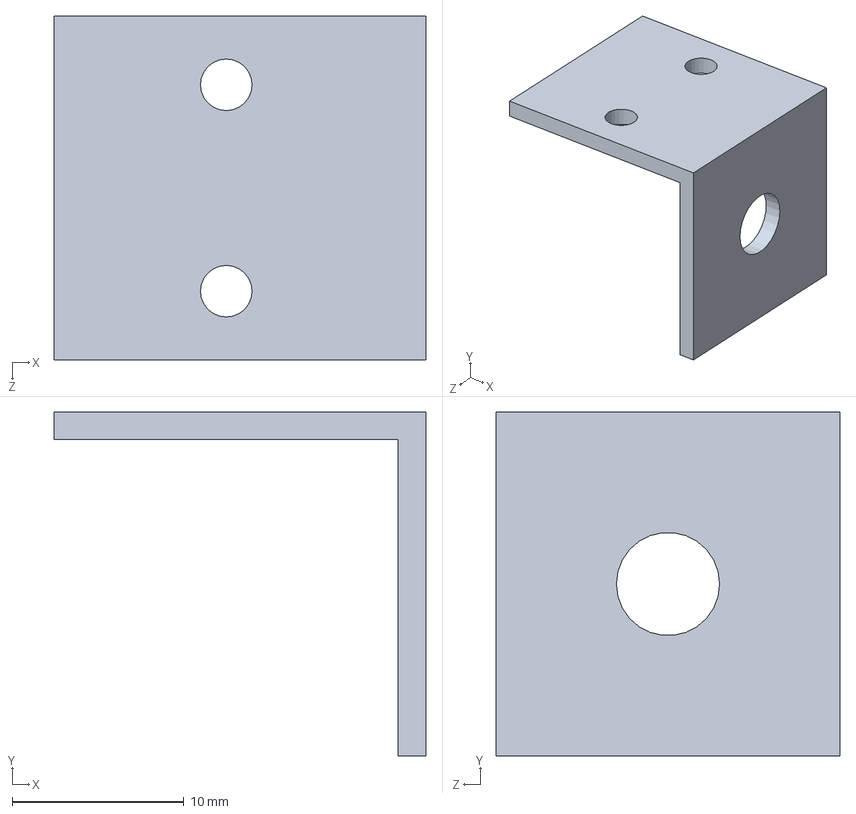
[picture p75: CAD file, 2019-07-15]
Solidworks/Rod2CBraketBraket.SLDPRT
21.6 x 20.0 x 20.0 mm
