sarvan13/Team9-Robot/Solidworks/spacer_drivetrain_small.SLDPRT

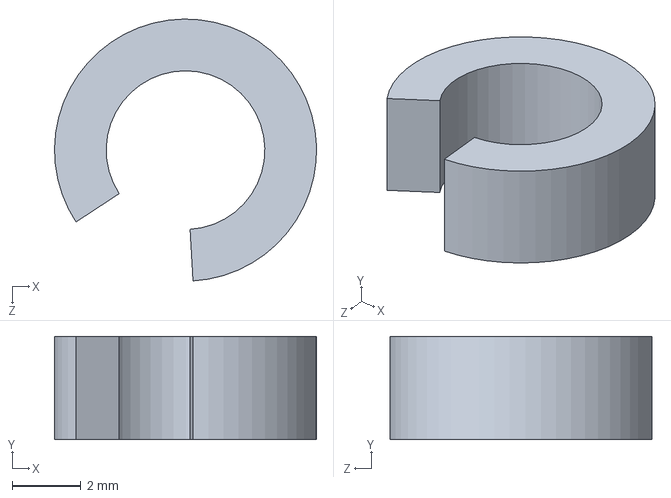
[picture p76: CAD file, 2019-07-15]
Solidworks/spacer_drivetrain_small.SLDPRT
7.60 x 3.00 x 7.59 mm
