sarvan13/Team9-Robot/Solidworks/iso_spur_platter_big.SLDPRT

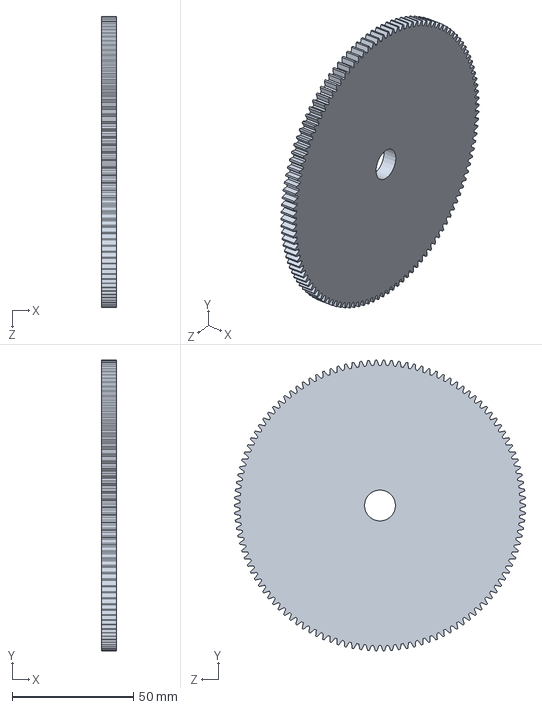
[picture p77: CAD file, 2019-07-15]
Solidworks/iso_spur_platter_big.SLDPRT
6.00 x 120.0 x 120.0 mm
