sarvan13/Team9-Robot/Solidworks/big_battery_holder.SLDPRT

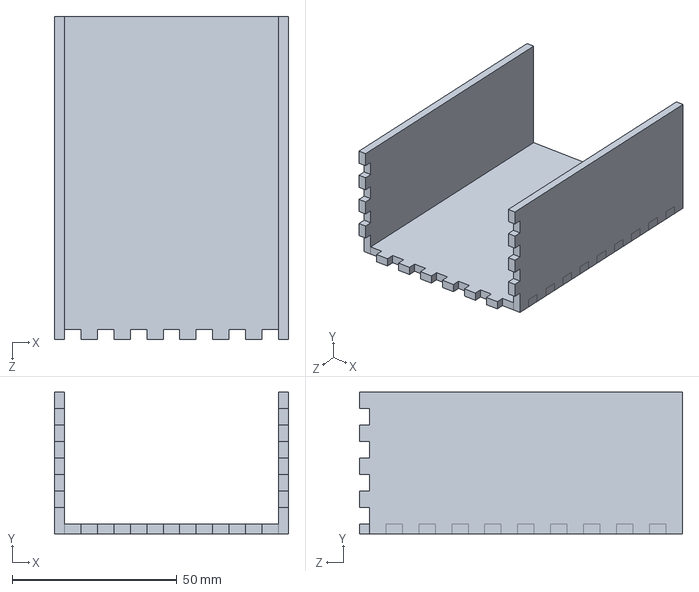
[picture p78: CAD file, 2019-07-15]
Solidworks/big_battery_holder.SLDPRT
71.0 x 43.0 x 98.0 mm
