sarvan13/Team9-Robot/Solidworks/iso_spur_drivetrain_big.SLDPRT

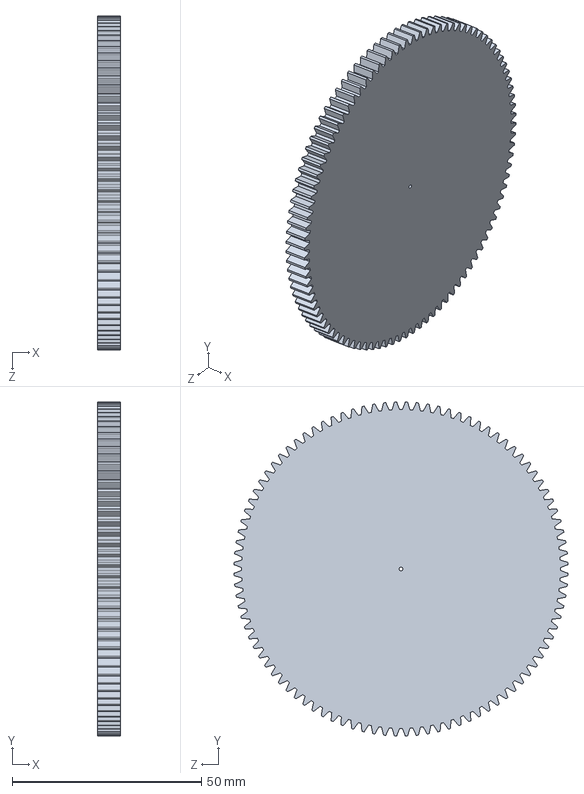
[picture p79: CAD file, 2019-07-15]
Solidworks/iso_spur_drivetrain_big.SLDPRT
6.00 x 88.2 x 88.2 mm
