sarvan13/Team9-Robot/Solidworks/small_battery_holder.SLDPRT

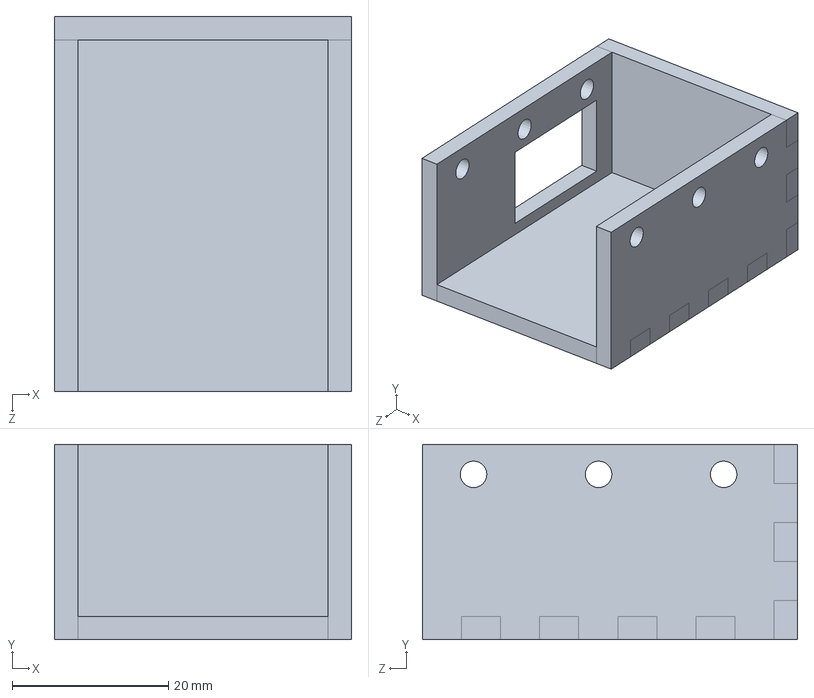
[picture p80: CAD file, 2019-07-15]
Solidworks/small_battery_holder.SLDPRT
38.0 x 25.0 x 48.0 mm
