sarvan13/Team9-Robot/Solidworks/arm_extension.SLDPRT

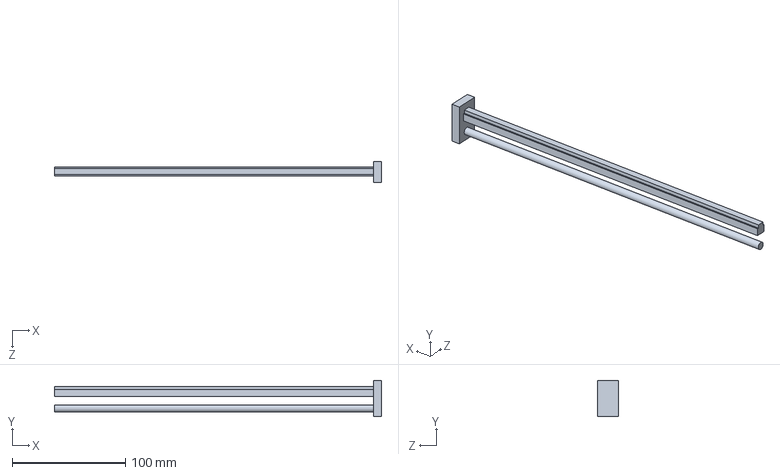
[picture p81: CAD file, 2019-07-15]
Solidworks/arm_extension.SLDPRT
289.0 x 32.1 x 18.9 mm
