sarvan13/Team9-Robot/Solidworks/lazy susan bearing.SLDPRT

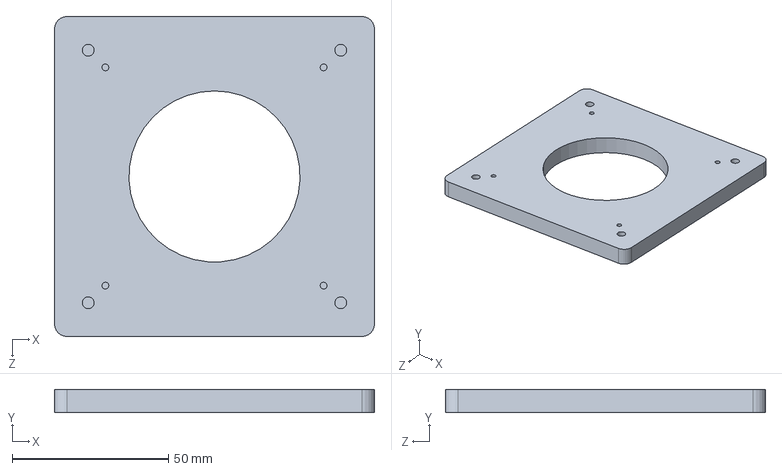
[picture p82: CAD file, 2019-07-15]
Solidworks/lazy susan bearing.SLDPRT
102.5 x 7.50 x 102.5 mm
