sarvan13/Team9-Robot/Solidworks/ServoMotor.SLDPRT

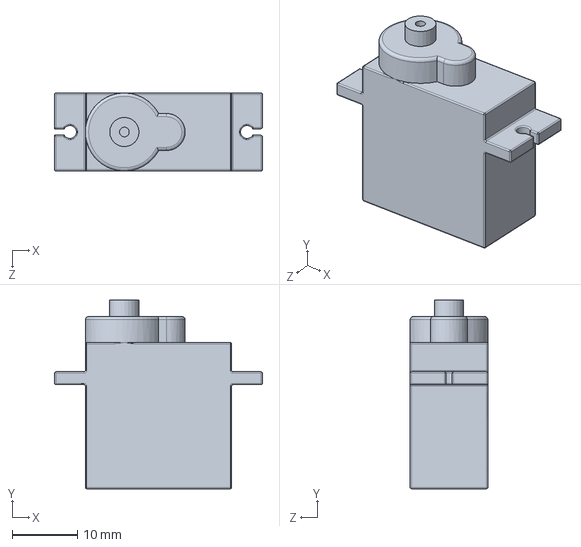
[picture p83: CAD file, 2019-07-15]
Solidworks/ServoMotor.SLDPRT
32.0 x 29.0 x 12.0 mm
