sarvan13/Team9-Robot/Solidworks/iso_spur_drivetrain_small.SLDPRT

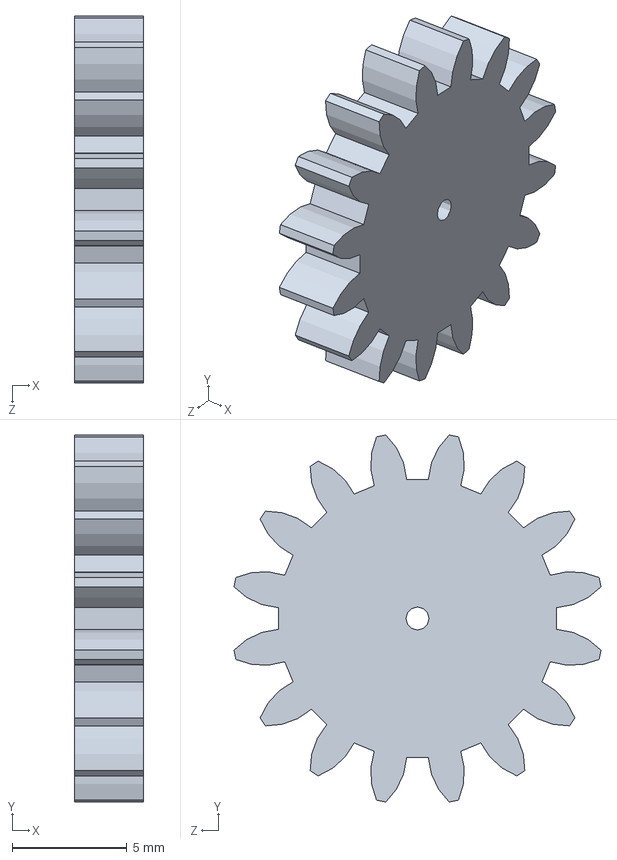
[picture p84: CAD file, 2019-07-15]
Solidworks/iso_spur_drivetrain_small.SLDPRT
3.00 x 16.0 x 16.0 mm
