sarvan13/Team9-Robot/Solidworks/NutPlateFlat.SLDPRT

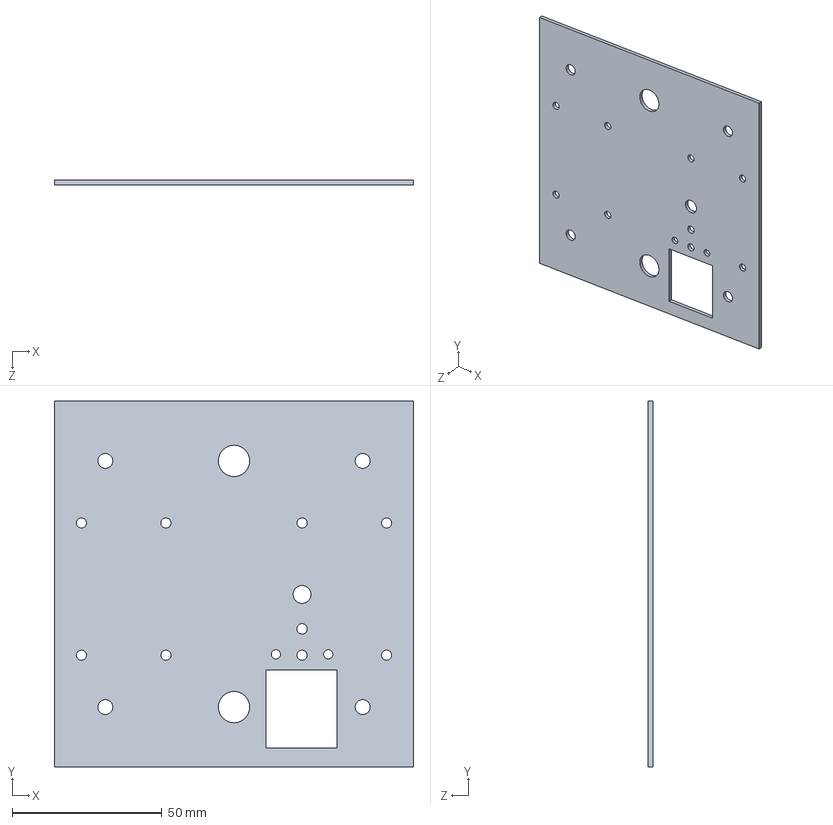
[picture p85: CAD file, 2019-07-15]
Solidworks/NutPlateFlat.SLDPRT
120.0 x 122.3 x 1.60 mm
