sarvan13/Team9-Robot/Solidworks/spacer_drivetrain_big.SLDPRT

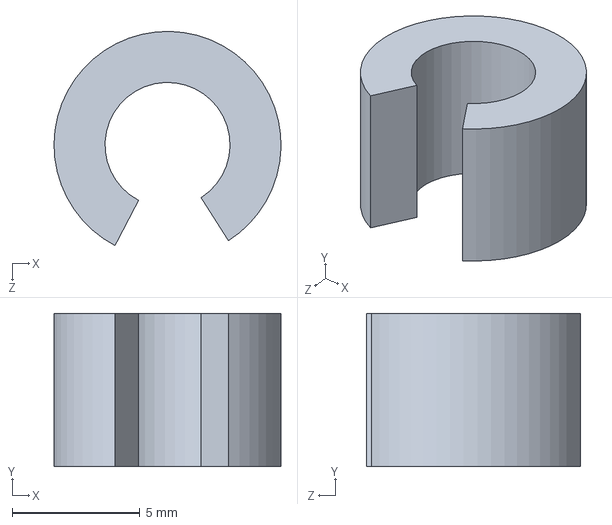
[picture p86: CAD file, 2019-07-15]
Solidworks/spacer_drivetrain_big.SLDPRT
8.90 x 6.00 x 8.39 mm
