sarvan13/Team9-Robot/Solidworks/RackOffset.DXF

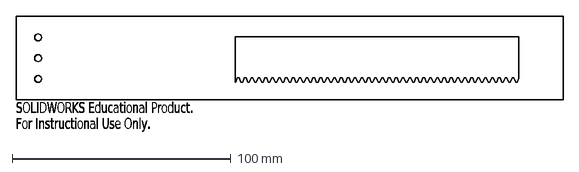
[picture p87: CAD file, 2019-07-14]
Solidworks/RackOffset.DXF
SOLIDWORKS Educational Product.
For Instructional Use Only.
