sarvan13/Team9-Robot/Solidworks/small_battery_holderSideYes.DXF

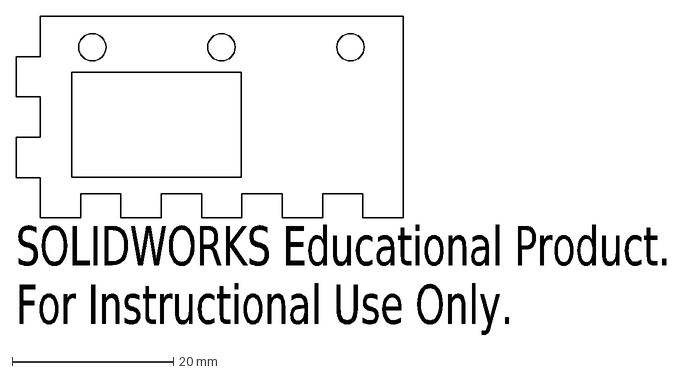
[picture p88: CAD file, 2019-07-12]
Solidworks/small_battery_holderSideYes.DXF
SOLIDWORKS Educational Product.
For Instructional Use Only.
