sarvan13/Team9-Robot/Solidworks/small_battery_holderSideNo.DXF

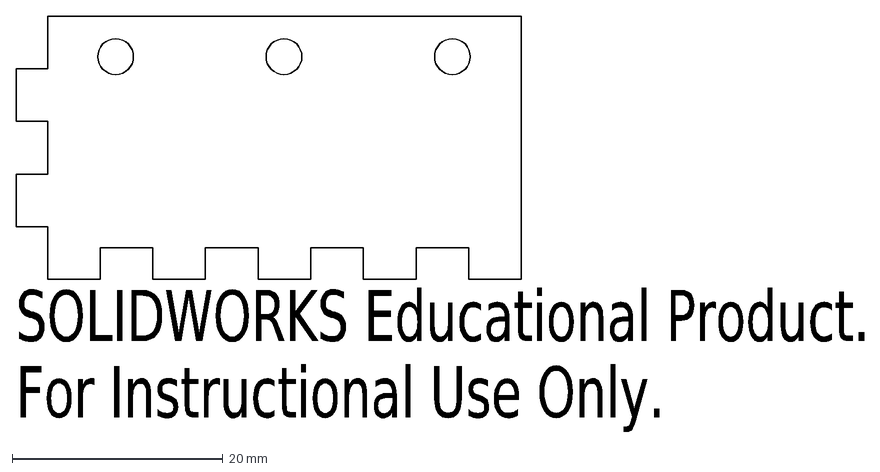
[picture p89: CAD file, 2019-07-12]
Solidworks/small_battery_holderSideNo.DXF
SOLIDWORKS Educational Product.
For Instructional Use Only.
