sarvan13/Team9-Robot/Solidworks/small_battery_holderBack.DXF

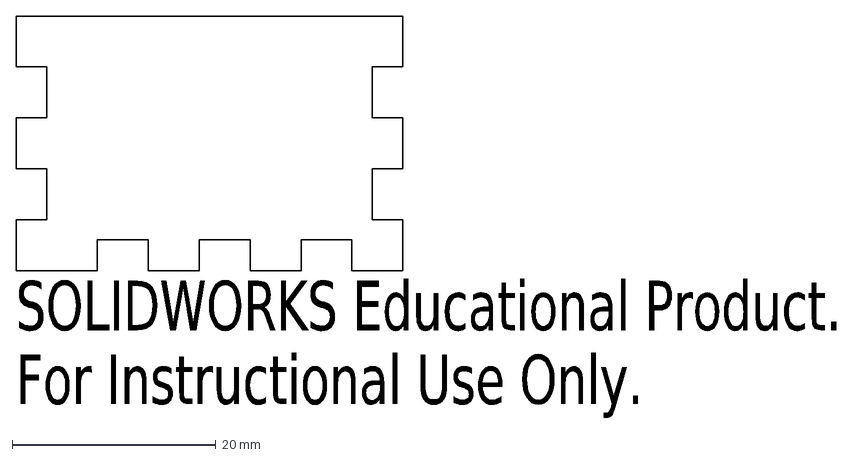
[picture p90: CAD file, 2019-07-12]
Solidworks/small_battery_holderBack.DXF
SOLIDWORKS Educational Product.
For Instructional Use Only.
