sarvan13/Team9-Robot/Solidworks/sidePiece.DXF

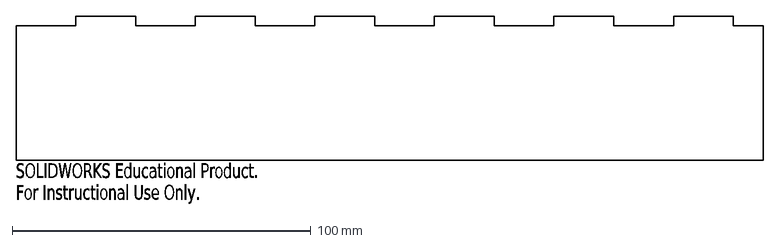
[picture p91: CAD file, 2019-06-20]
Solidworks/sidePiece.DXF
SOLIDWORKS Educational Product.
For Instructional Use Only.
