sarvan13/Team9-Robot/Solidworks/topChassis.DXF

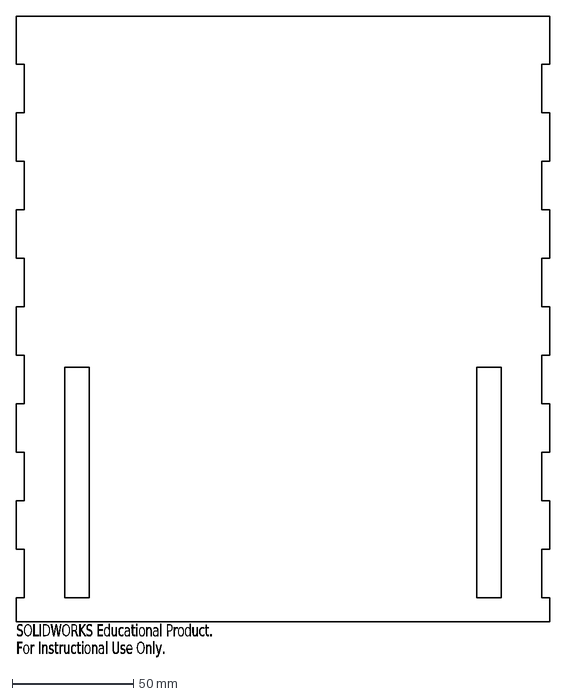
[picture p92: CAD file, 2019-06-20]
Solidworks/topChassis.DXF
SOLIDWORKS Educational Product.
For Instructional Use Only.
