sarvan13/Team9-Robot/slave_code/src/ArmMovement.h

// #define ARMMOVEMENT_H

// class ArmMovement
// {
//     public:
//         void side_2_side(int num_ticks);
//         void up_down(int distance); //mm
//         void in_n_out(int distance); //mm
//         void go_far_in_n_out();
//         void go_home_in_n_out();
//         void go_home_up_down(); 
//         void go_home_side_2_side();
//     private:
//         int reg_speed;
// };

// #endif //ARMMOVEMENT_H
