sarvan13/Team9-Robot/robot_test_code/src/Movement.h

#ifndef MOVEMENT_H
#define MOVEMENT_H

class Movement
{
    public:
        Movement();
        void turn_left();
        void turn_right();
        void u_turn();
        void reverse(int left_speed, int right_speed);
        void forward();
        void apply_pid(int pid);
        void grab_plushie_left();
        void grab_plushie_right();
        void grab_plushie_front();
        void stop();
        void set_speed(int speed);
        void rotate_left(int speed);
        void rotate_right(int speed);
        void alternate_pid(int pid);
    
    private:
        int reg_speed;
};

enum movement_amount
{
    CONTINUOUS = -1, 
    NINETY_DEGREES = 1230,
};
#endif //MOVEMENT_H
